mzeitler/openstrom/schematic/source - draft/Altium-CPU-board-multi/Cross-section-sketch2.PcbDoc.htm

Reporting Options

# File in Previous Format

Date | : | 24.06.2016
Time | : | 16:26:15
Filename | : | C:\Users\Matthias E. Zeitler\Documents\Business\Open Strom\Github\openstrom\schematic\source - draft\Altium-CPU-board-multi\Cross-section-sketch2.PcbDoc

Version | Warning

This file was generated by an earlier version of the software
