mzeitler/openstrom/docs/OpenStrom - Pitch - Oct 2015.pdf

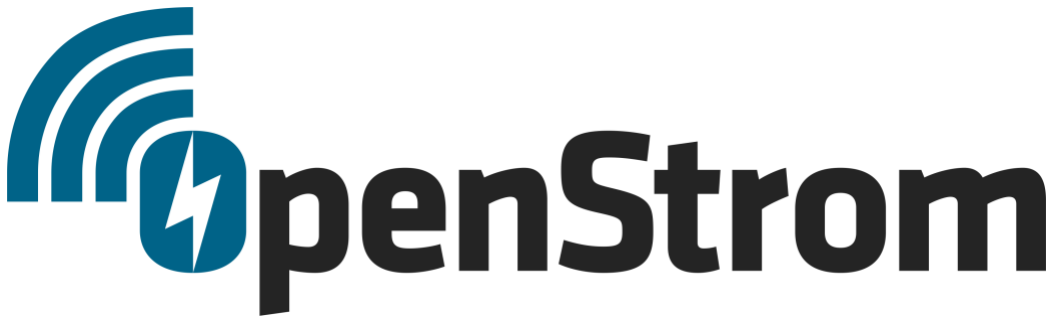
[picture p21: figure]

# The Open Hardware Smart Meter

# that powers the smart energy revolution

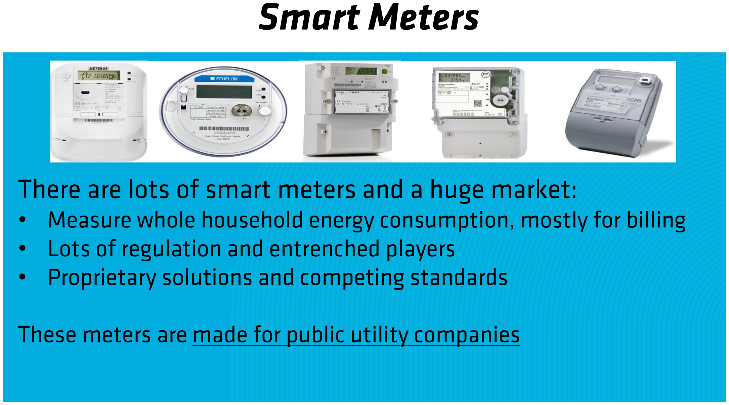
[picture p22: page 2]

•••

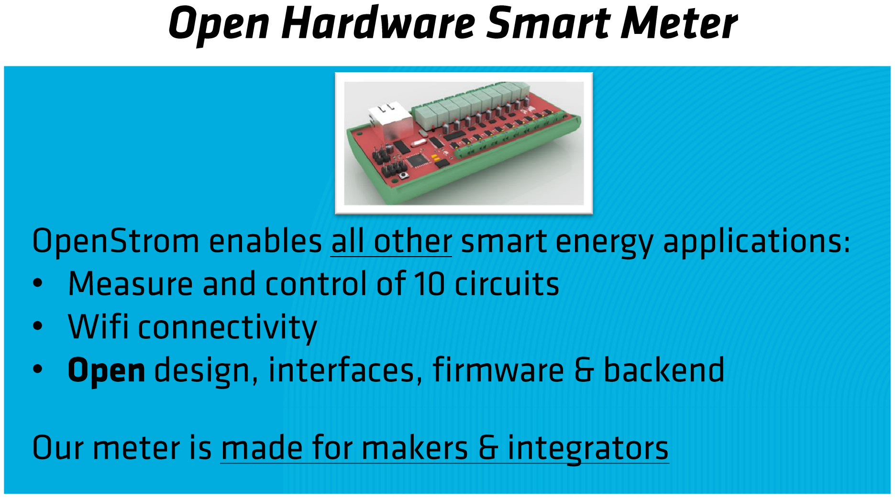
[picture p23: page 3]

•••

Component | Characteristics
MCU | 80 MHz 512k kB + 128 MB
Connectivity | LAN, Wifi ZigBee
Sensors | Voltage, current, mean active power, mean reactive power, voltage frequency, power factor, phase angle between voltage and current, mean apparent power 90 - 250 V AC 0 – 40A 7.4 kHz sampling
Relays (10x) | Switching up to 40A at 250V, max. 10kW
Form factor | DIN rail compatible housing (for mounting inside fuse box)

### Operating temperature range: 0°C to 85°C (commercial)

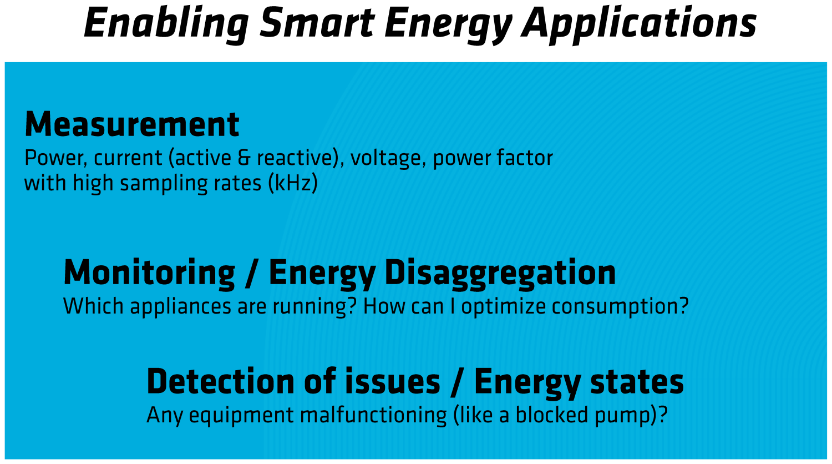
[picture p24: page 5]

•••

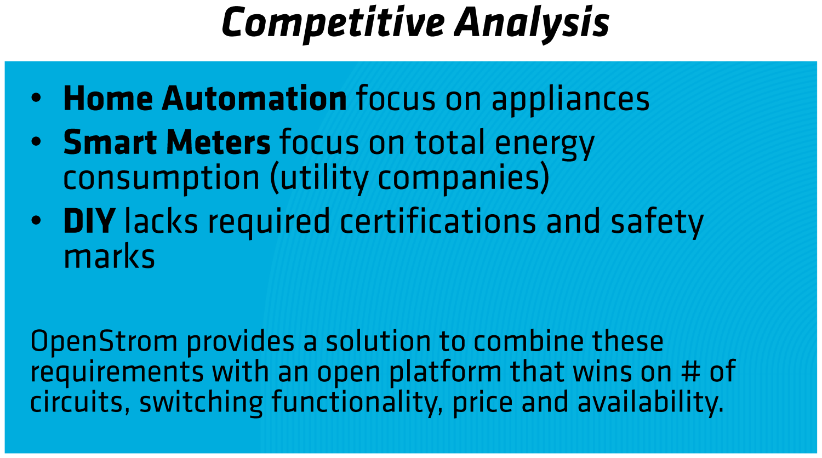
[picture p25: page 6]

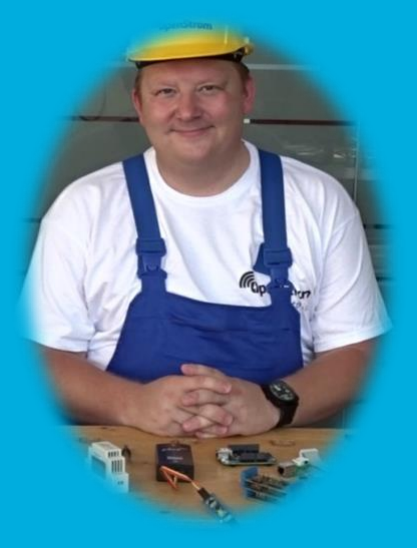
[picture p26: figure]
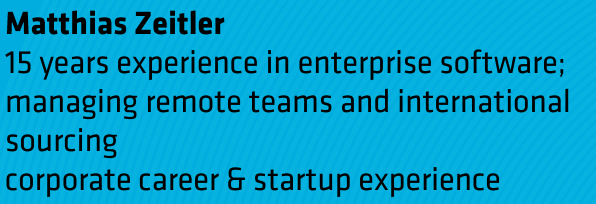
[picture p27: figure]

Engineering team to build prototype:
Tony Tachev, 20 years experience as embedded engineer designing with microcontrollers Franklin Francis, 5 years experience with firmware development and prototyping
plus identified candidates for software development

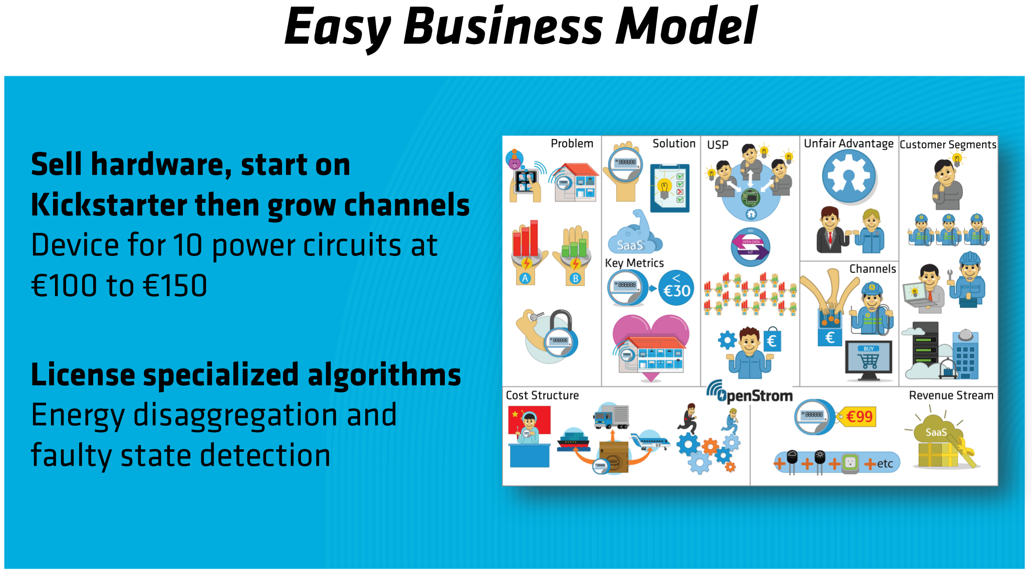
[picture p28: page 8]
