mzeitler/openstrom/housing/v0.1 - initial ideas/1 (1).JPG

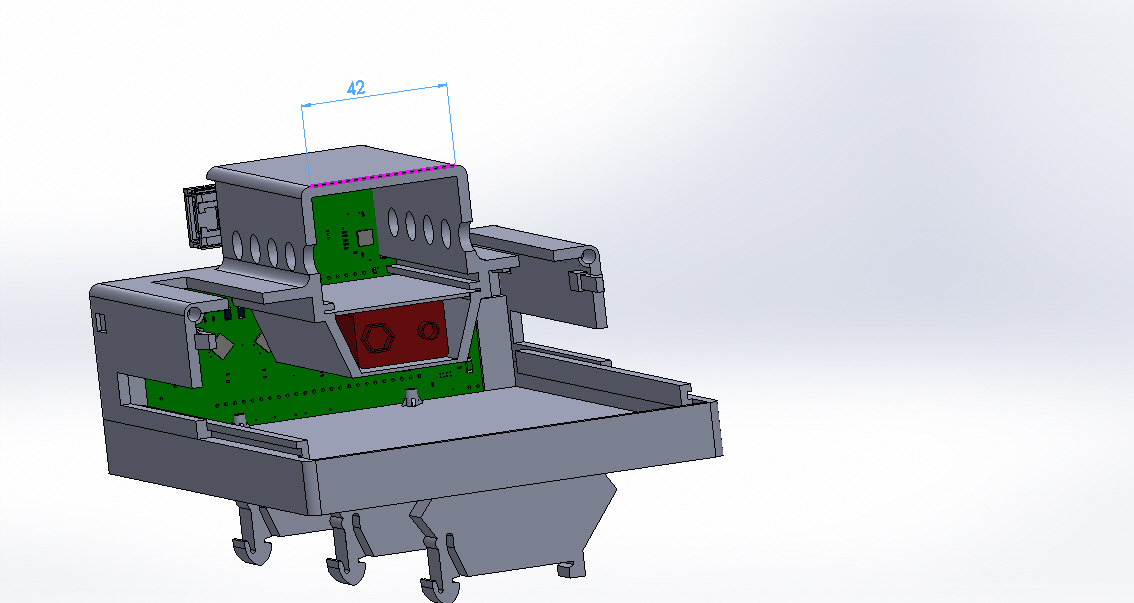
housing/v0.1 - initial ideas/1 (1).JPG
