mzeitler/openstrom/housing/v0.1 - initial ideas/2.jpg

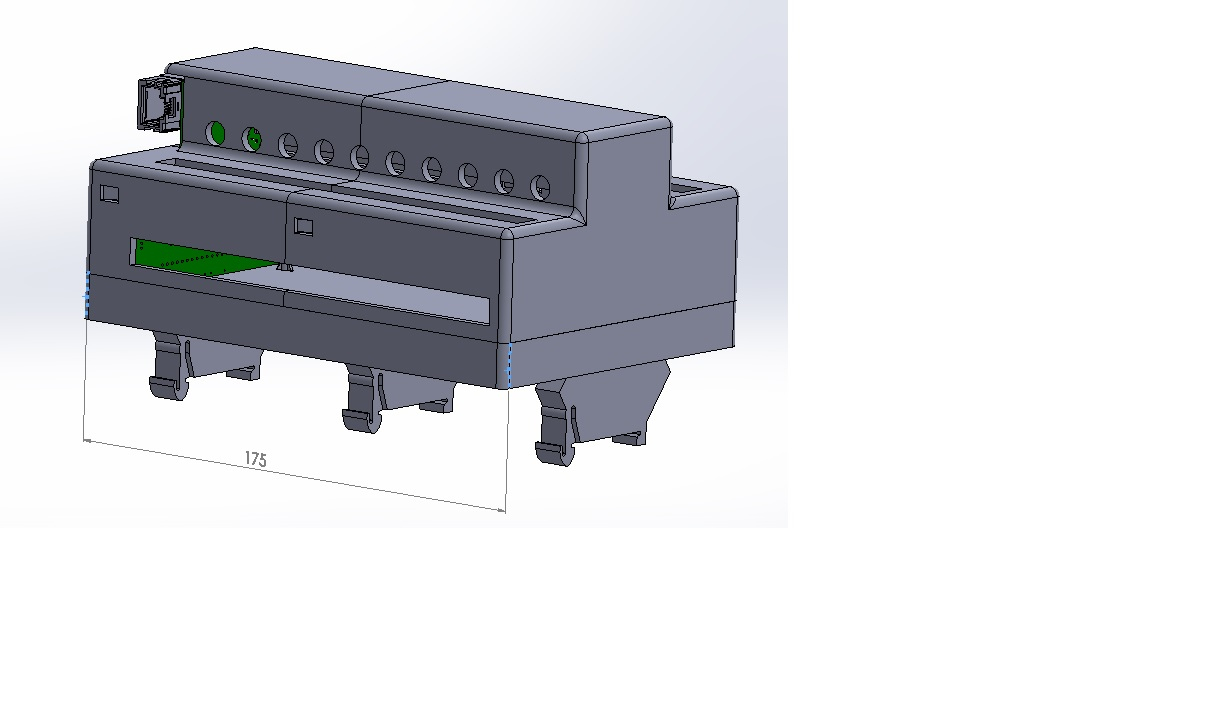
housing/v0.1 - initial ideas/2.jpg
