mzeitler/openstrom/housing/v0.1 - initial ideas/3.JPG

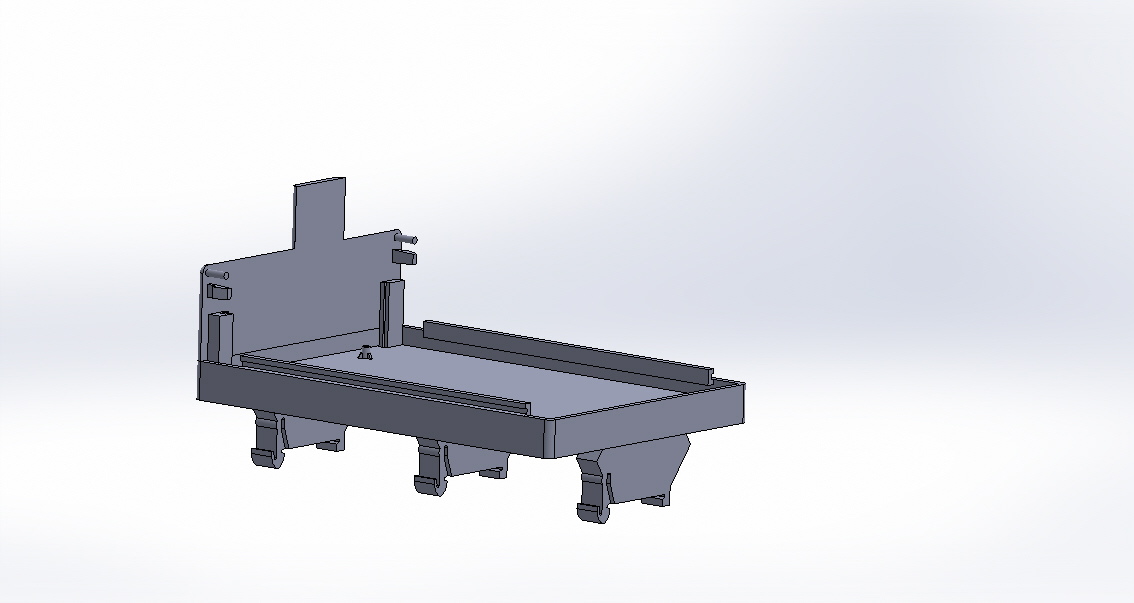
housing/v0.1 - initial ideas/3.JPG
