mzeitler/openstrom/housing/v0.1 - initial ideas/4.JPG

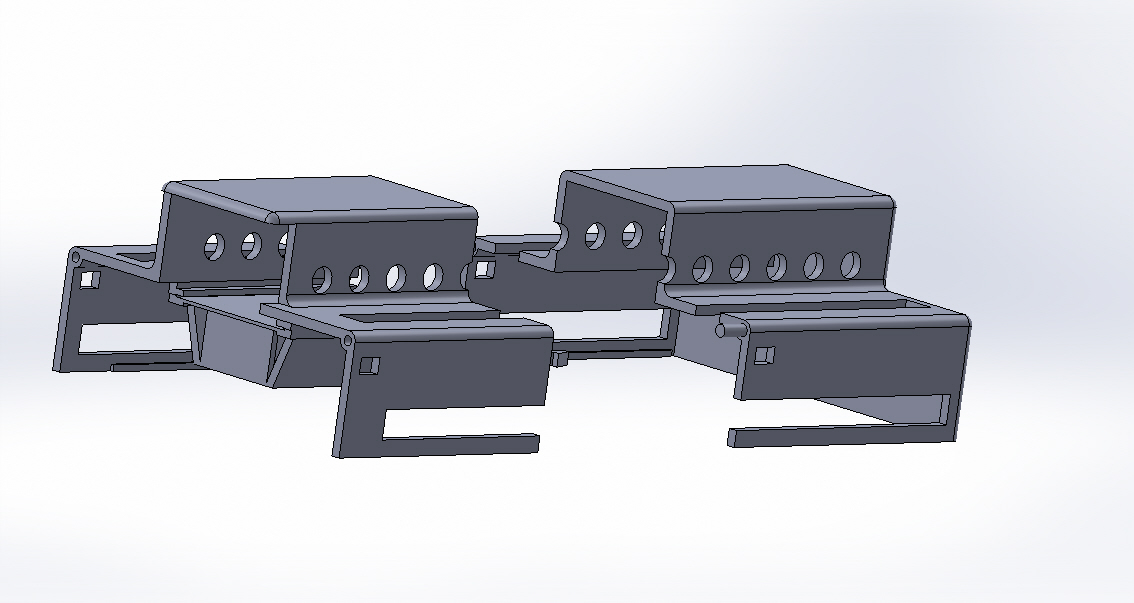
housing/v0.1 - initial ideas/4.JPG
