mzeitler/openstrom/housing/v0.1 - initial ideas/5.JPG

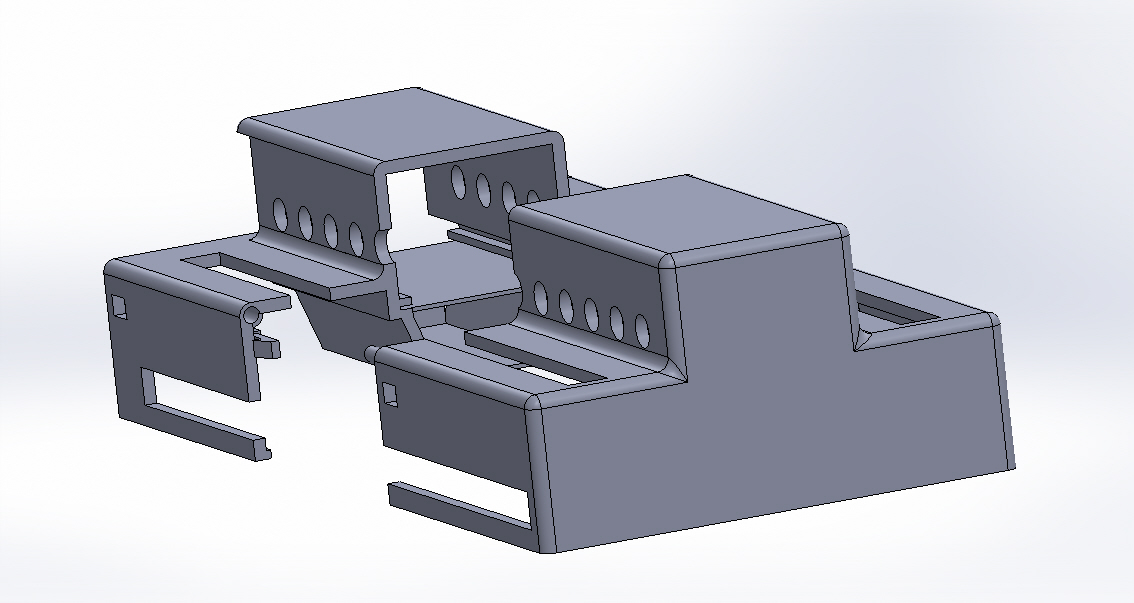
housing/v0.1 - initial ideas/5.JPG
