mzeitler/openstrom/housing/v0.1 - initial ideas/CT_BOARD.jpg

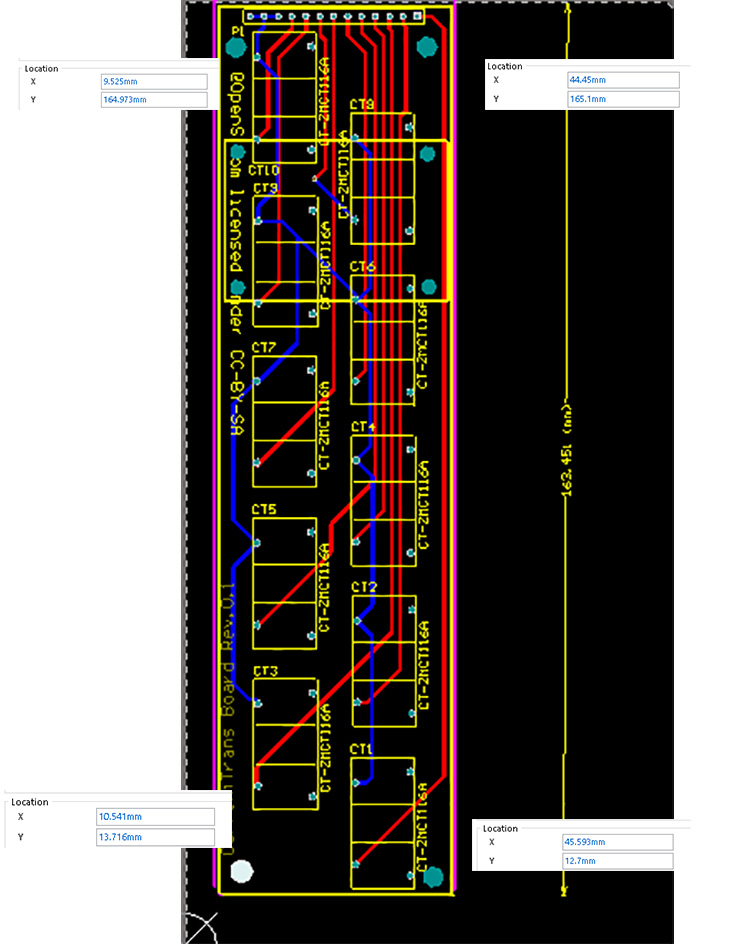
housing/v0.1 - initial ideas/CT_BOARD.jpg
