mzeitler/openstrom/housing/v0.1 - initial ideas/Final Exploded view-1.JPG

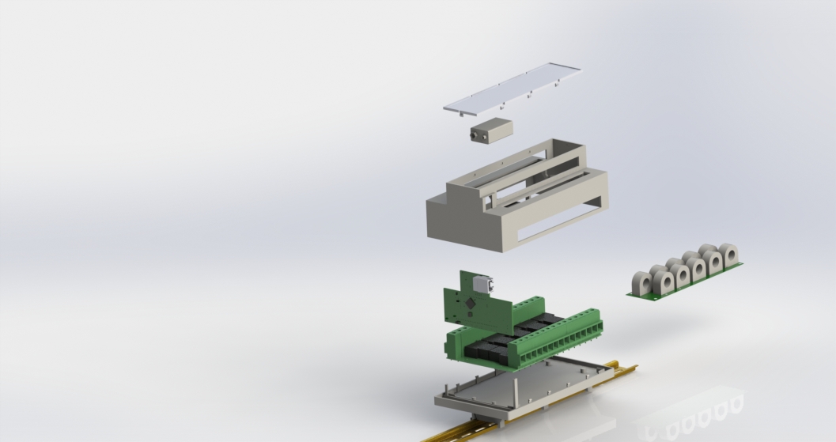
housing/v0.1 - initial ideas/Final Exploded view-1.JPG
