mzeitler/openstrom/housing/v0.1 - initial ideas/Final Exploded view-2.JPG

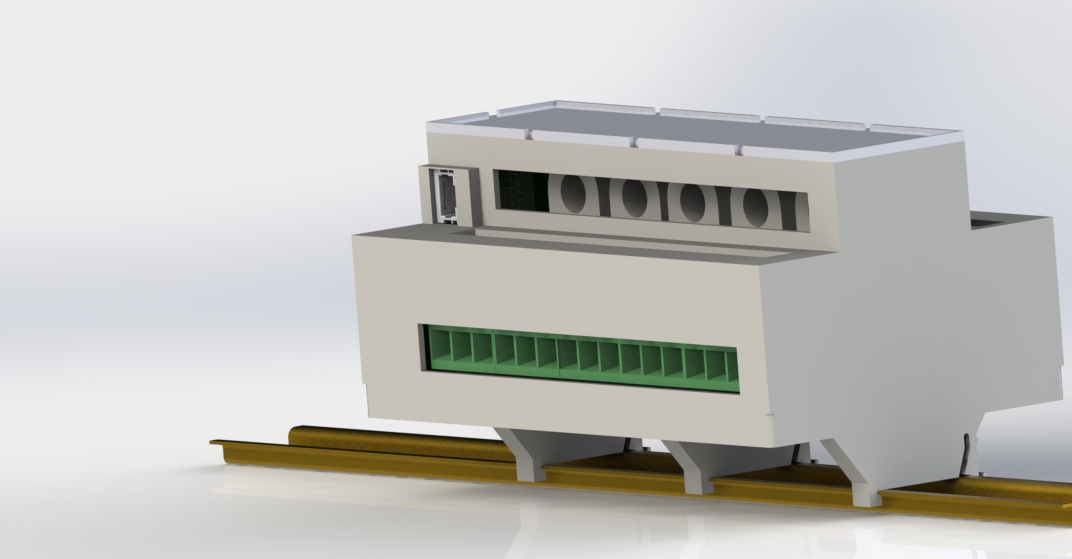
housing/v0.1 - initial ideas/Final Exploded view-2.JPG
