mzeitler/openstrom/housing/v0.1 - initial ideas/Relay_BOARD_H.jpg

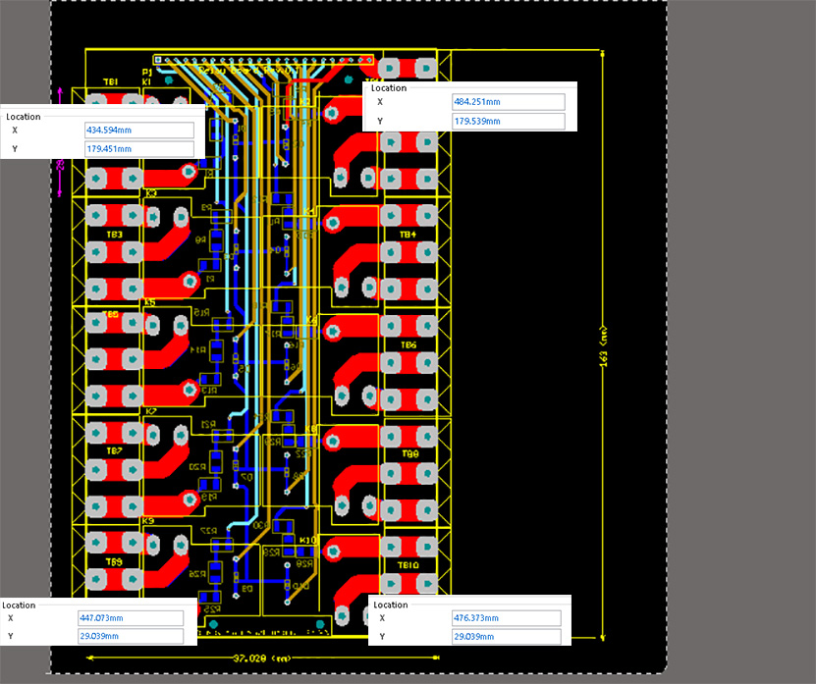
housing/v0.1 - initial ideas/Relay_BOARD_H.jpg
