mzeitler/openstrom/housing/v0.2 - design for prototpye/Ethernet Port View.JPG

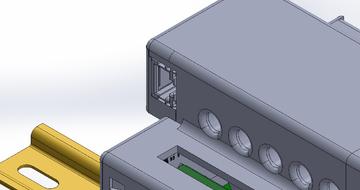
housing/v0.2 - design for prototpye/Ethernet Port View.JPG
