mzeitler/openstrom/housing/v0.2 - design for prototpye/Part2.JPG

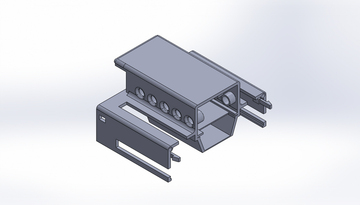
housing/v0.2 - design for prototpye/Part2.JPG
