mzeitler/openstrom/housing/v0.2 - design for prototpye/Part3.JPG

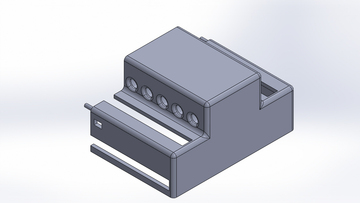
housing/v0.2 - design for prototpye/Part3.JPG
