mzeitler/openstrom/housing/v0.3 - prototype/CIMG8475.JPG

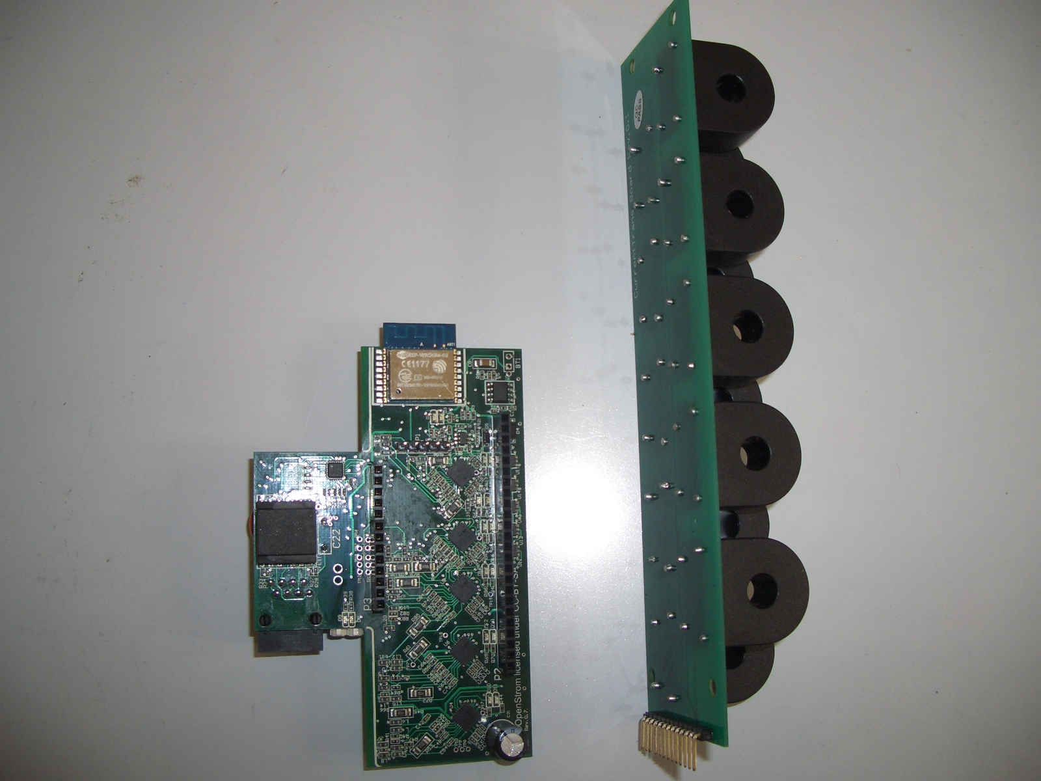
housing/v0.3 - prototype/CIMG8475.JPG
