mzeitler/openstrom/housing/v0.3 - prototype/CIMG8476.JPG

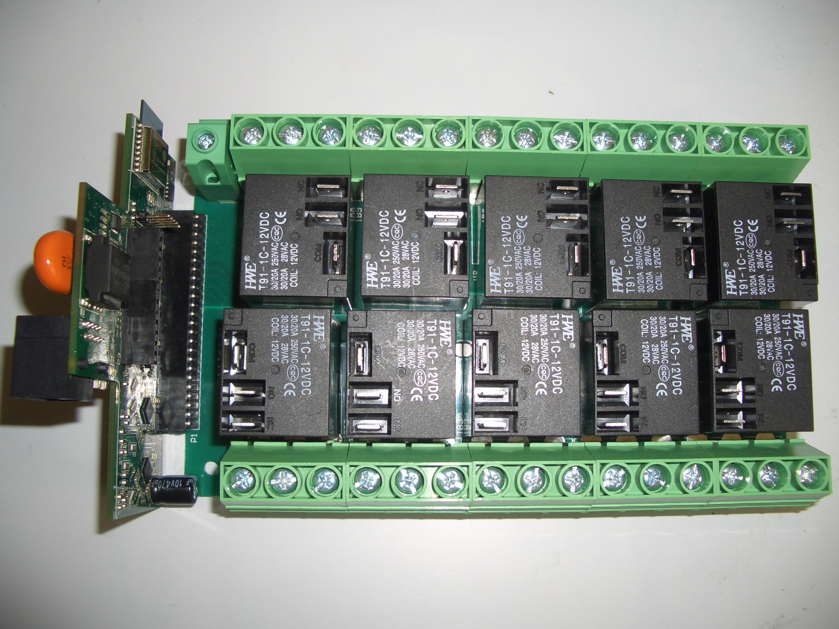
housing/v0.3 - prototype/CIMG8476.JPG
