mzeitler/openstrom/housing/v0.3 - prototype/CIMG8477.JPG

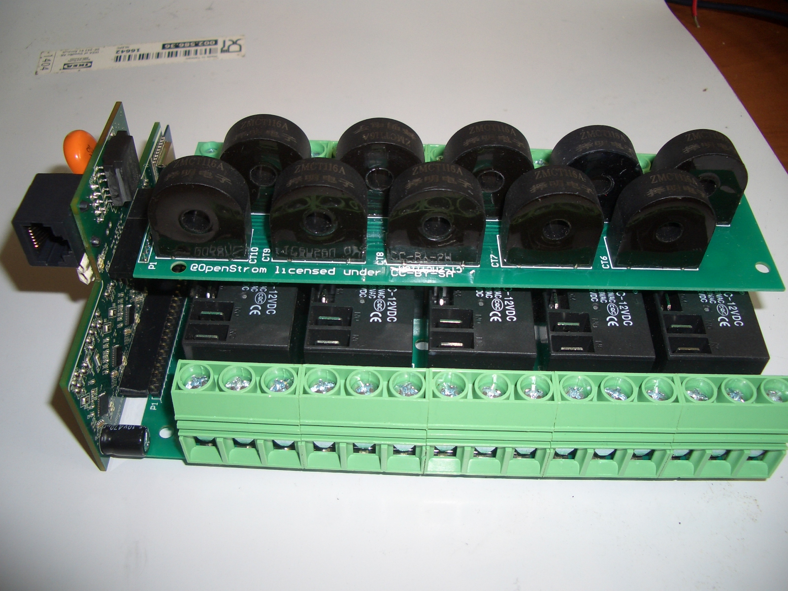
housing/v0.3 - prototype/CIMG8477.JPG
