mzeitler/openstrom/housing/v0.3 - prototype/CIMG8479.JPG

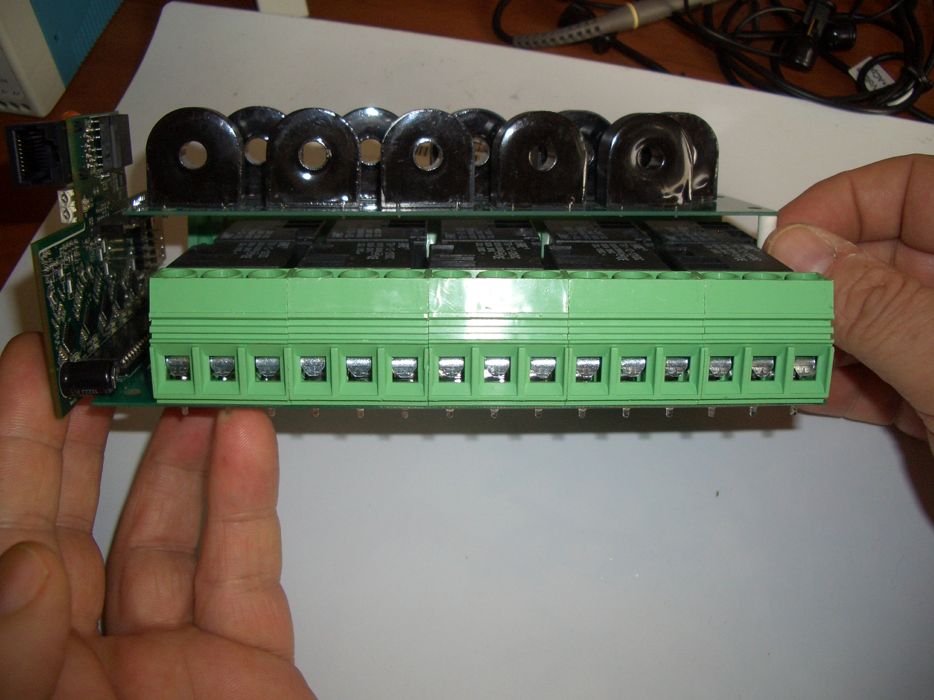
housing/v0.3 - prototype/CIMG8479.JPG
