mzeitler/openstrom/housing/v0.4 - prototype 2/18955070_1875733002680077_9011409751416302212_o.jpg

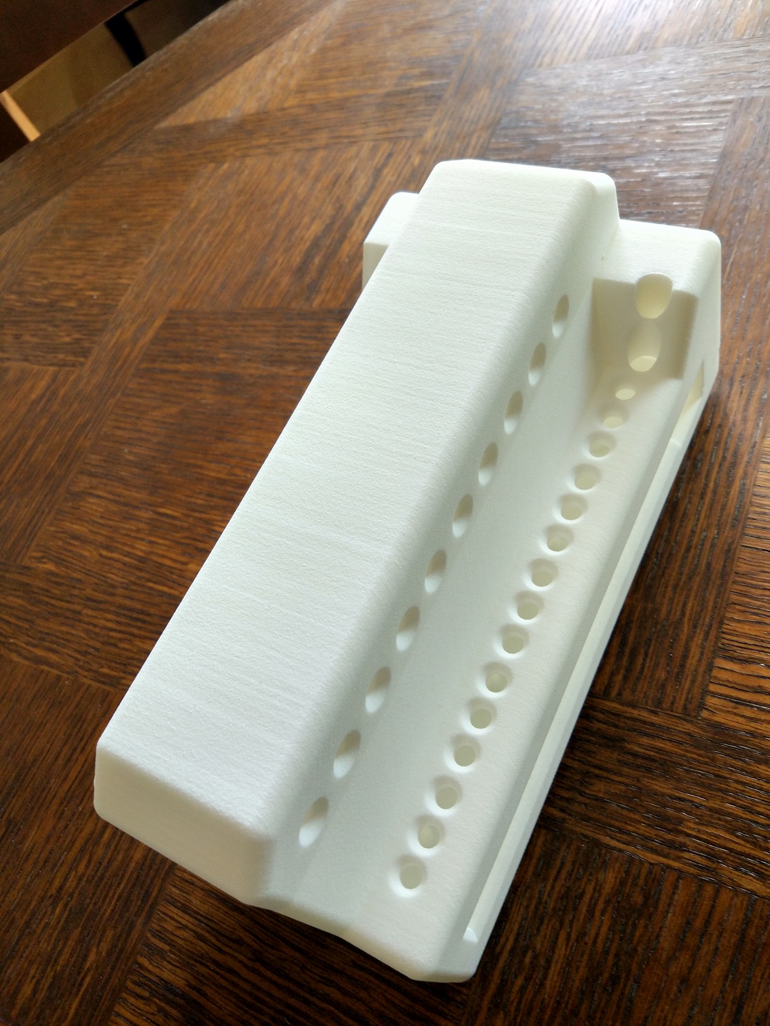
housing/v0.4 - prototype 2/18955070_1875733002680077_9011409751416302212_o.jpg
