mzeitler/openstrom/housing/v0.4a - Lasercut/18891693_1875733032680074_797341241410242619_o.jpg

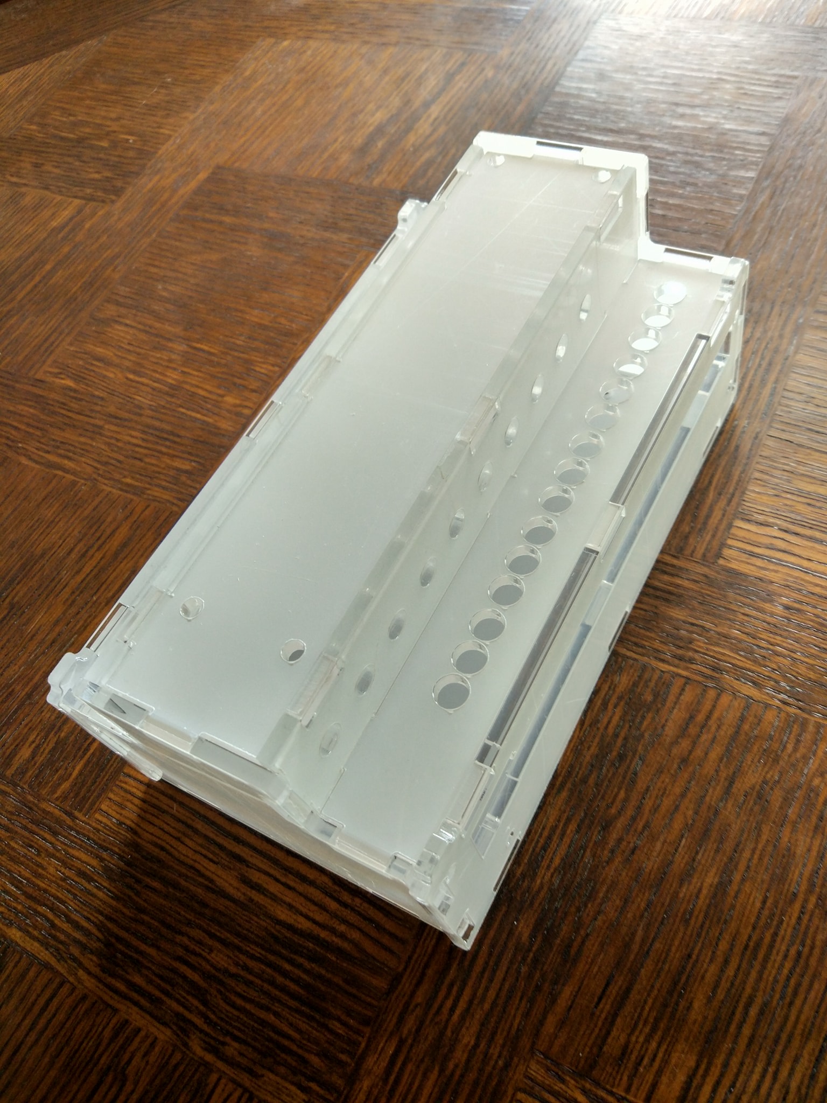
housing/v0.4a - Lasercut/18891693_1875733032680074_797341241410242619_o.jpg
