mzeitler/openstrom/housing/v0.4 - prototype 2/assembled/2017-06-19 10.52.02.jpg

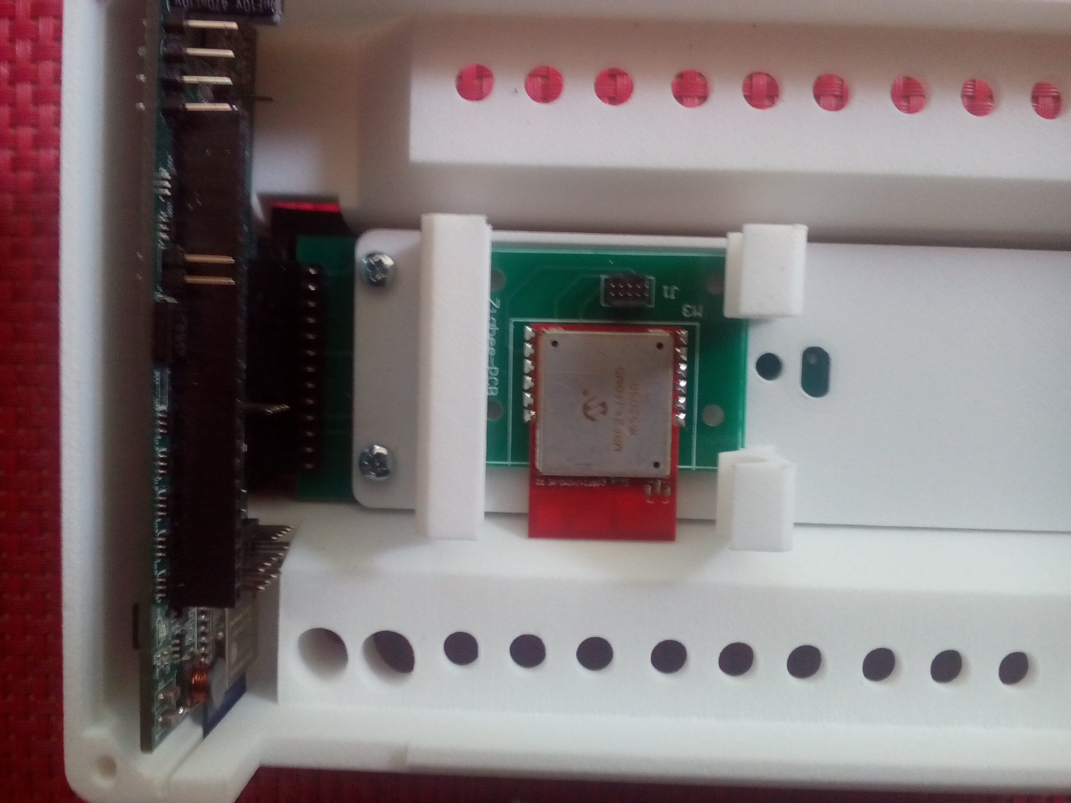
housing/v0.4 - prototype 2/assembled/2017-06-19 10.52.02.jpg
