mzeitler/openstrom/housing/v0.4 - prototype 2/assembled/2017-06-19 11.23.50.jpg

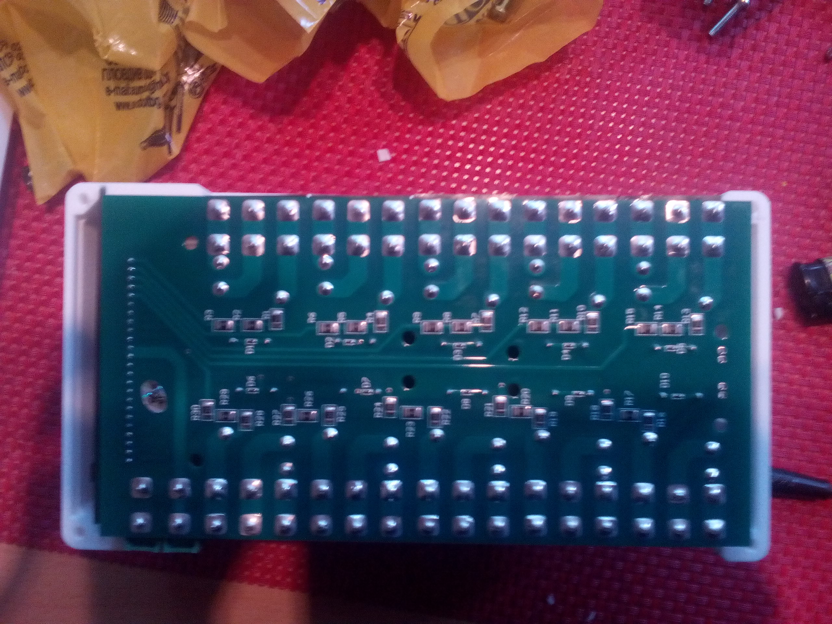
housing/v0.4 - prototype 2/assembled/2017-06-19 11.23.50.jpg
