mzeitler/openstrom/housing/v0.4 - prototype 2/assembled/2017-06-19 11.59.24.jpg

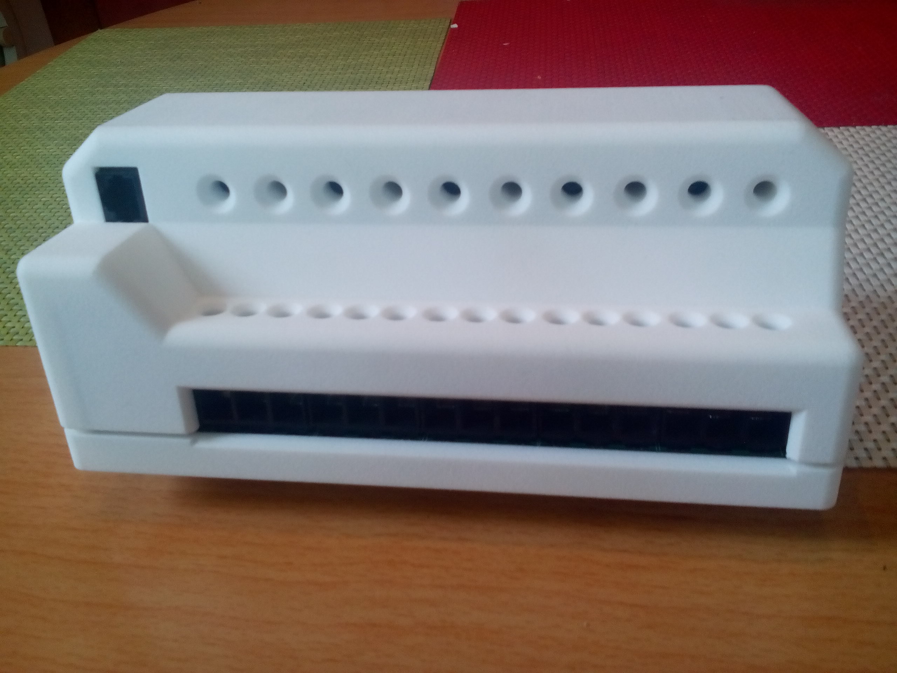
housing/v0.4 - prototype 2/assembled/2017-06-19 11.59.24.jpg
