mzeitler/openstrom/schematic/source - draft/PDF - for reference only/RelayBoard-Sch-multi.pdf

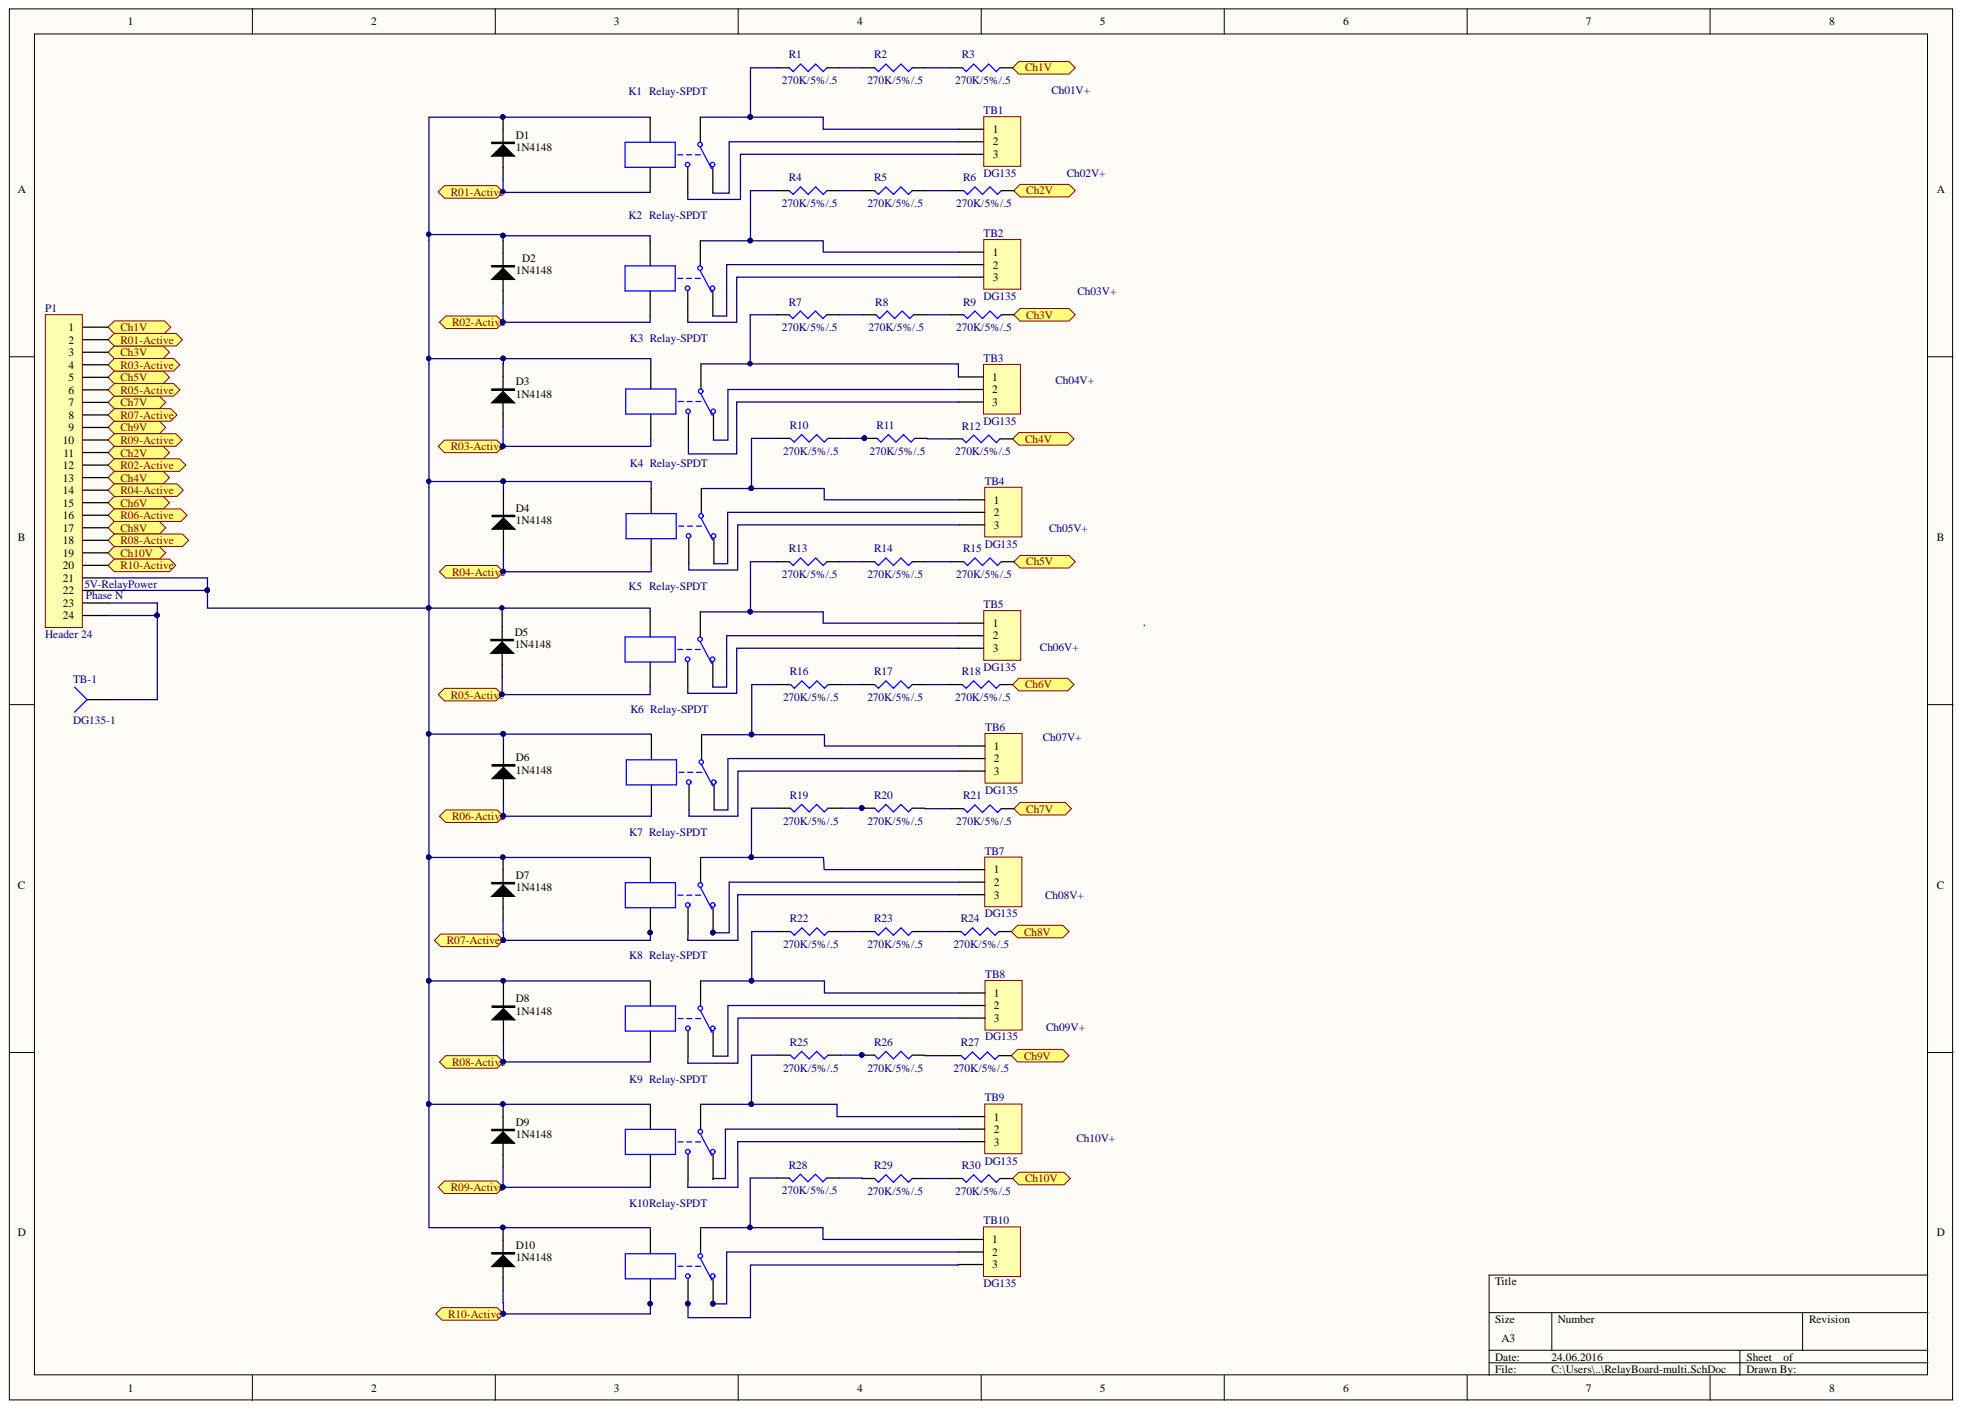
[picture p106: page 1]

5V-RelayPower
Phase N
