mzeitler/openstrom/housing/v0.1 - initial ideas/(Top Panel _2 - Sheet1.pdf

8 | 7 | 6 | 5 | 4 | 3 | 2 | 1

E

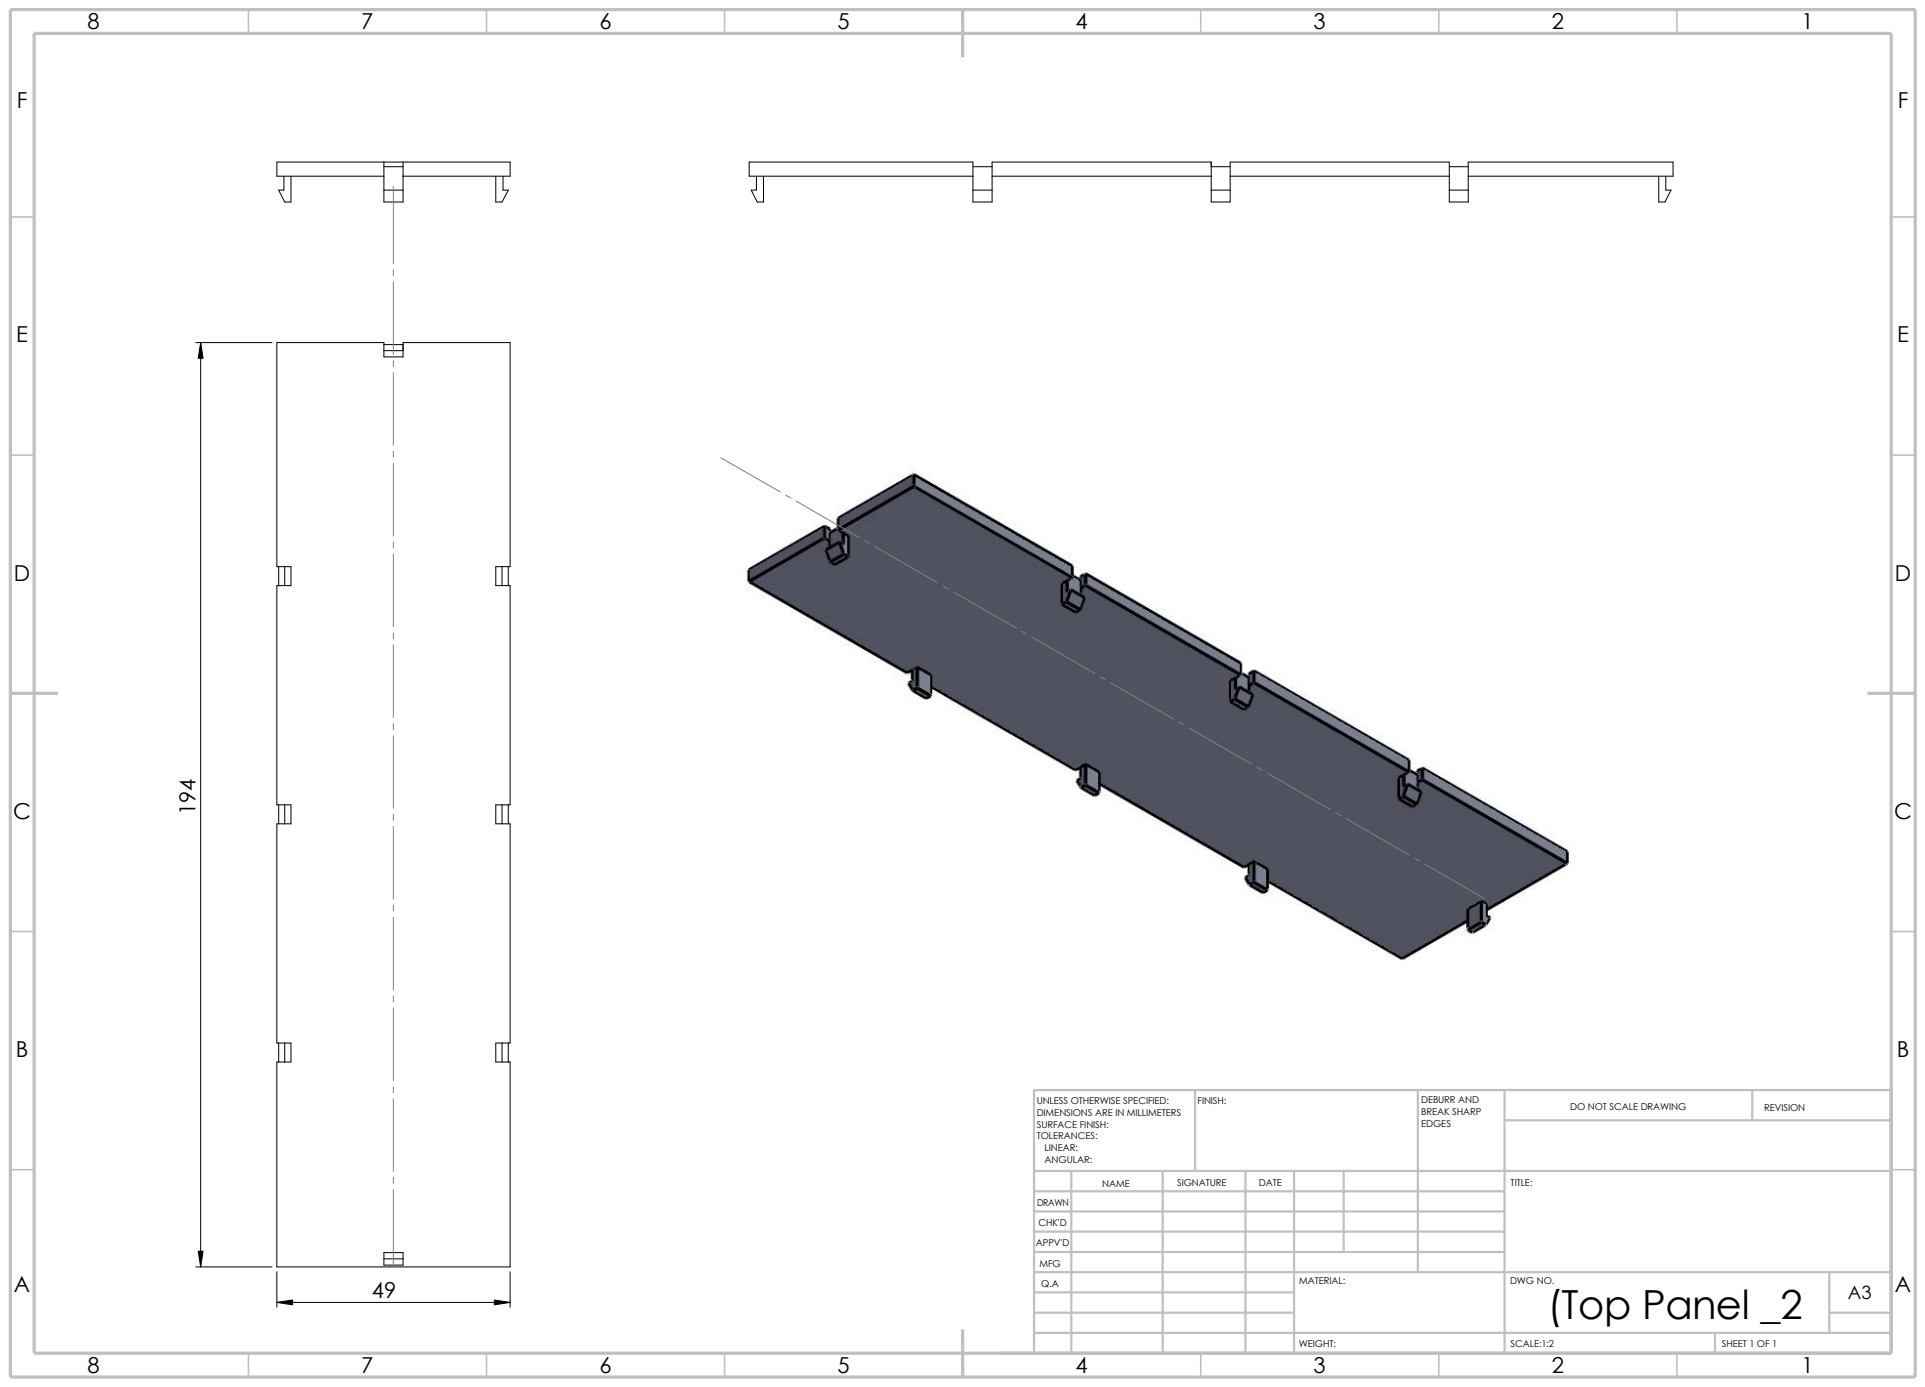
[picture p107: page 1]
WEIGHT:; SCALE:1:2; SHEET 1 OF 1; REVISION; FINISH:; EDGES; DEBURR AND BREAK SHARP

DO NOT SCALE DRAWING UNLESS OTHERWISE SPECIFIED:
DIMENSIONS ARE IN MILLIMETERS
SURFACE FINISH:
TOLERANCES:
LINEAR:
ANGULAR:

NAME | SIGNATURE | DATE | | | | TITLE:

DRAWN

CHK'D

APPV'D

MFG
Q.A | | | | MATERIAL: | DWG NO. | A3

(Top Panel _2 ⁴⁹
