mzeitler/openstrom/housing/v0.1 - initial ideas/base - Sheet1.pdf

8 | 7 | 6 | 5 | 4 | 3 | 2 | 1

E

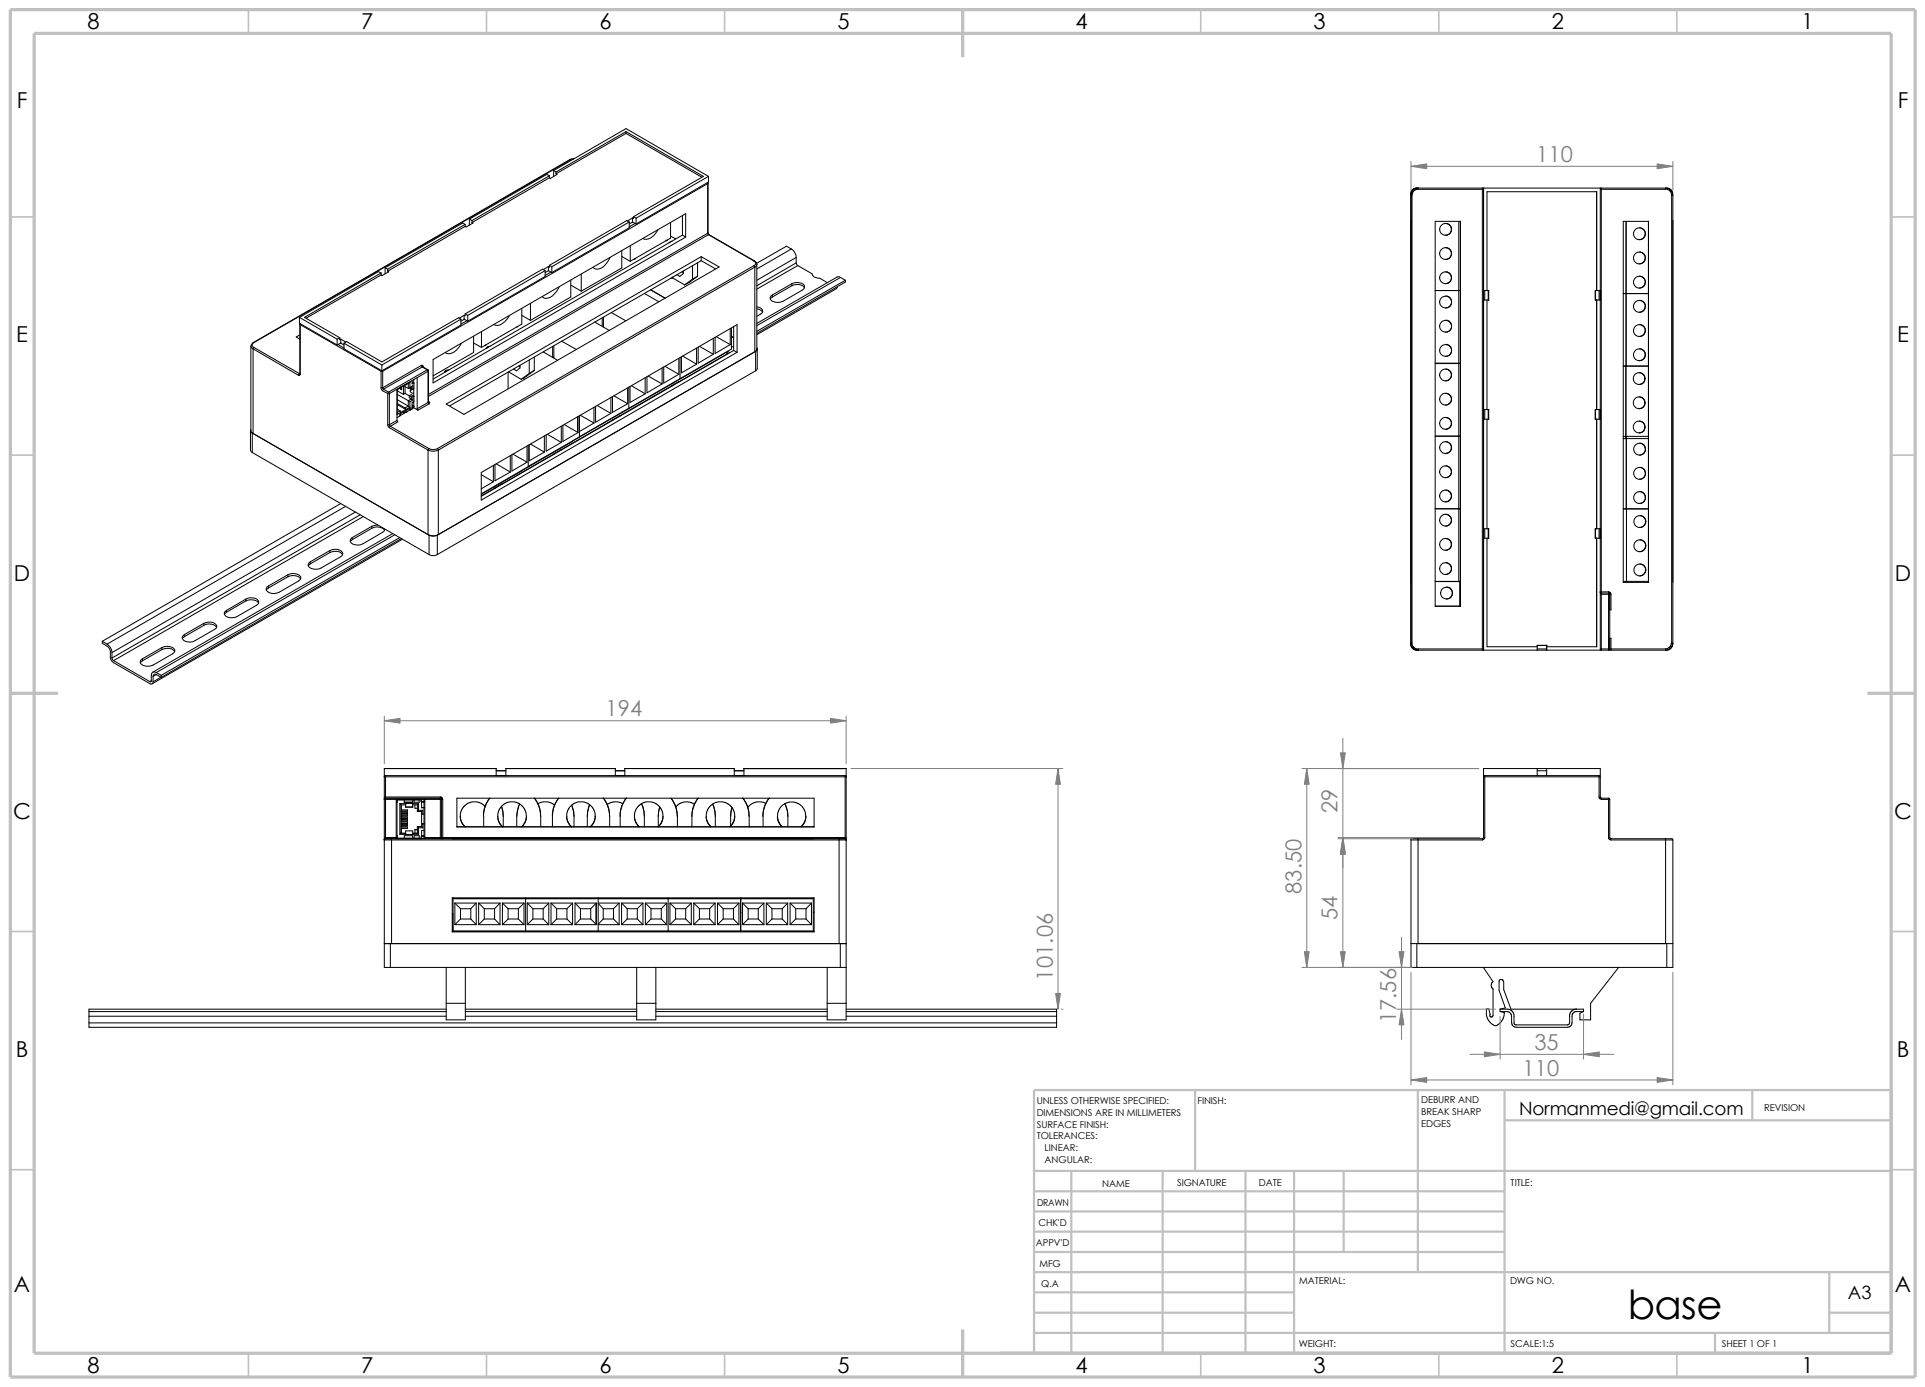
[picture p108: page 1]
WEIGHT:; SCALE:1:5; SHEET 1 OF 1; Normanmedi@gmail.com; REVISION UNLESS OTHERWISE SPECIFIED:

DIMENSIONS ARE IN MILLIMETERS SURFACE FINISH: TOLERANCES: LINEAR: ANGULAR: | FINISH: | DEBURR AND BREAK SHARP EDGES

NAME | SIGNATURE | DATE | | | | TITLE:

DRAWN

CHK'D

APPV'D

MFG

Q.A | | | | MATERIAL: | DWG NO. base | A3
