mzeitler/openstrom/housing/v0.1 - initial ideas/main_5 - Sheet1.pdf

8 | 7 | 6 | 5 | 4 | 3 | 2 | 1

E

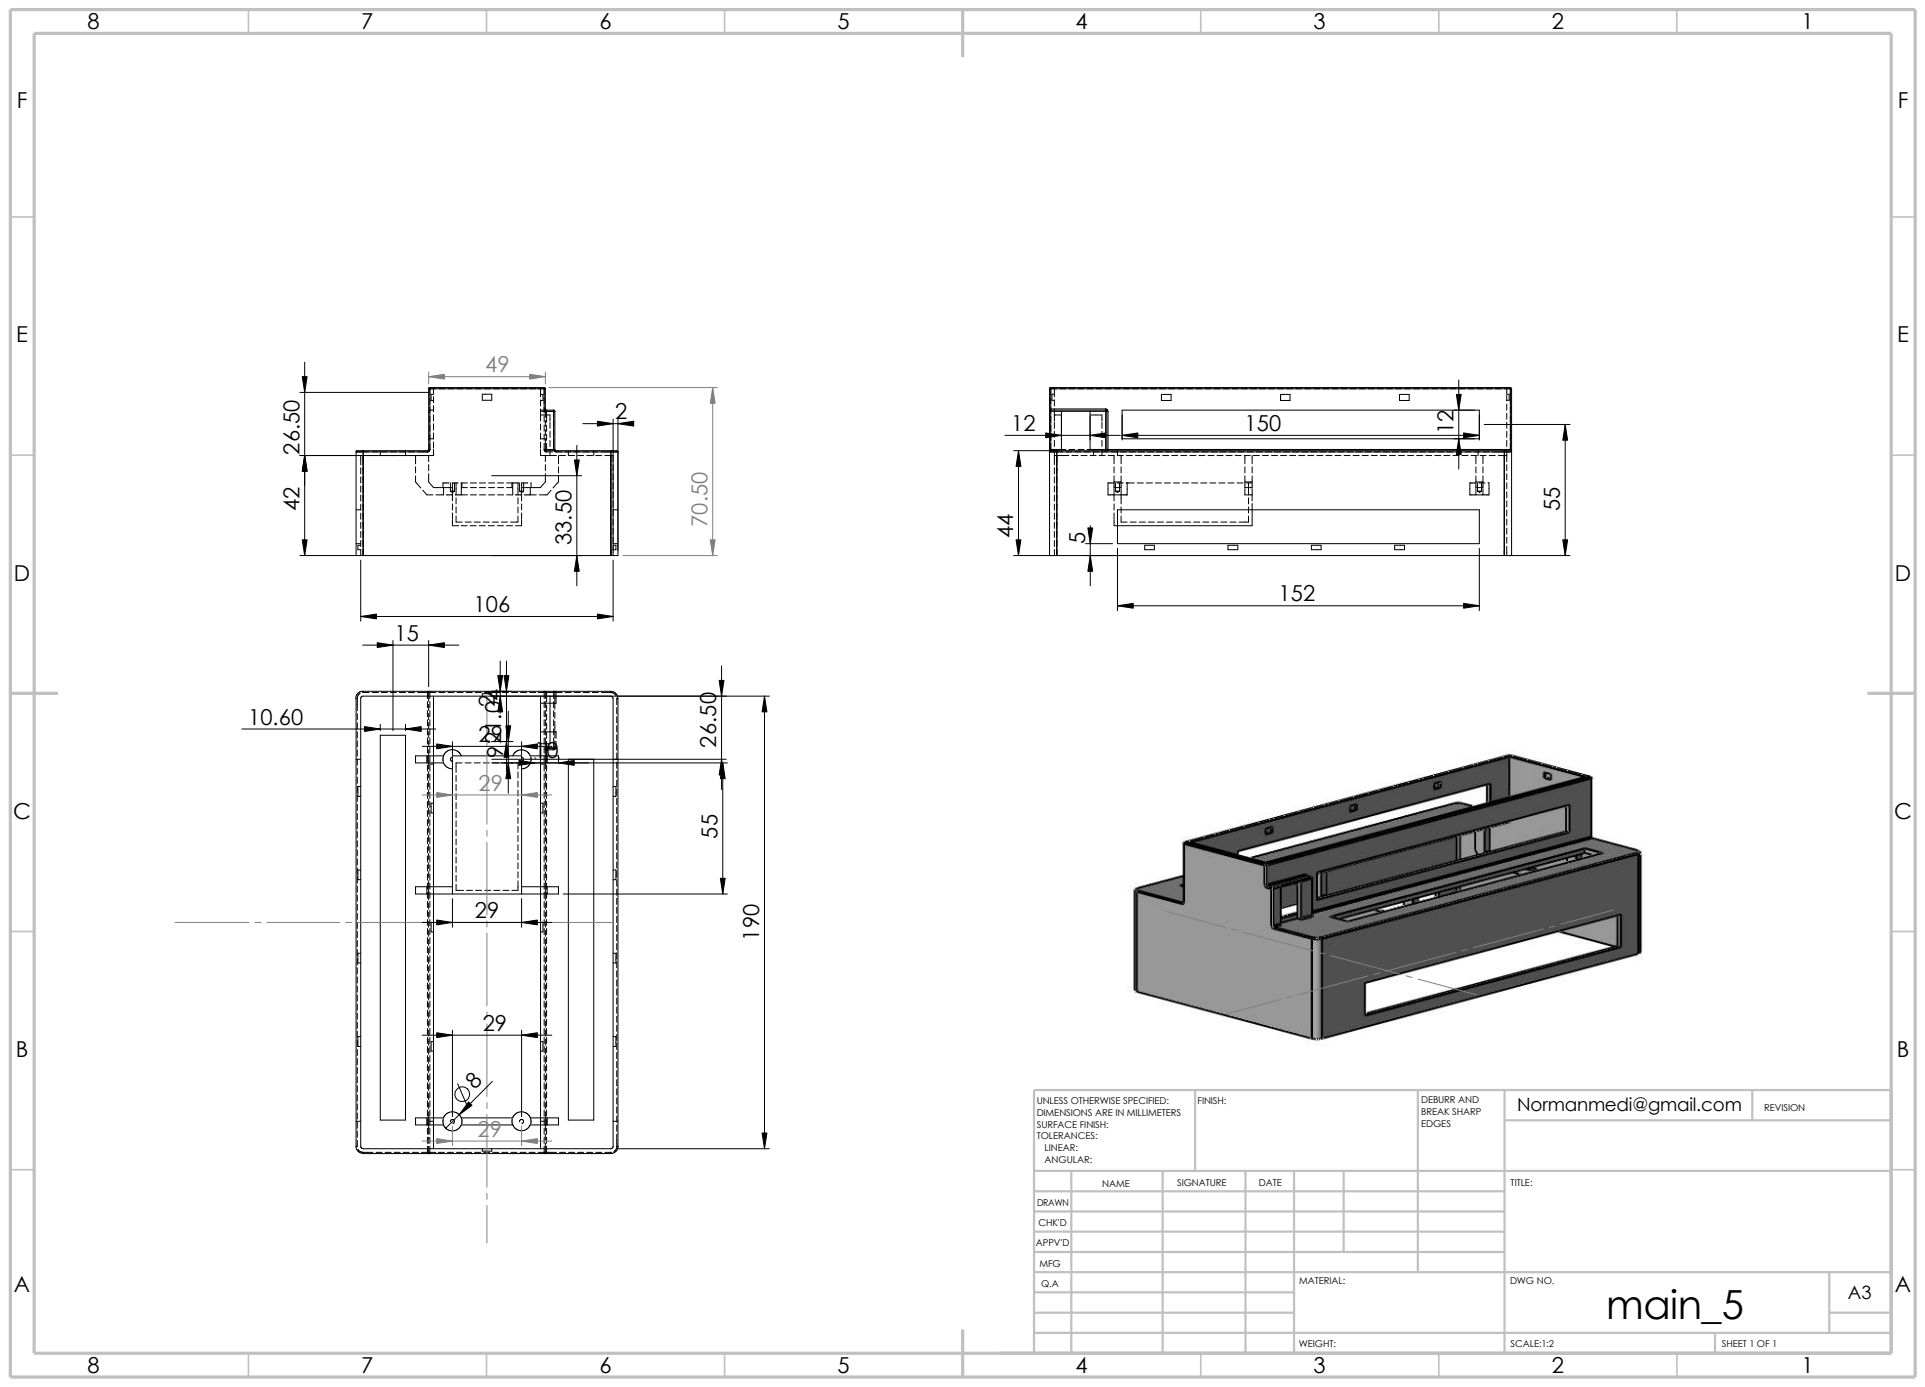
[picture p109: page 1]
WEIGHT:; SCALE:1:2; SHEET 1 OF 1; Normanmedi@gmail.com; REVISION UNLESS OTHERWISE SPECIFIED:

29
10

DIMENSIONS ARE IN MILLIMETERS SURFACE FINISH: TOLERANCES: LINEAR: ANGULAR: | FINISH: | DEBURR AND BREAK SHARP EDGES

NAME | SIGNATURE | DATE | | | | TITLE:

DRAWN

CHK'D

APPV'D

MFG

Q.A | | | | MATERIAL: | DWG NO. main_5 | A3
