mzeitler/openstrom/housing/v0.1 - initial ideas/Part2-2 - Sheet1.pdf

2 | 1

B

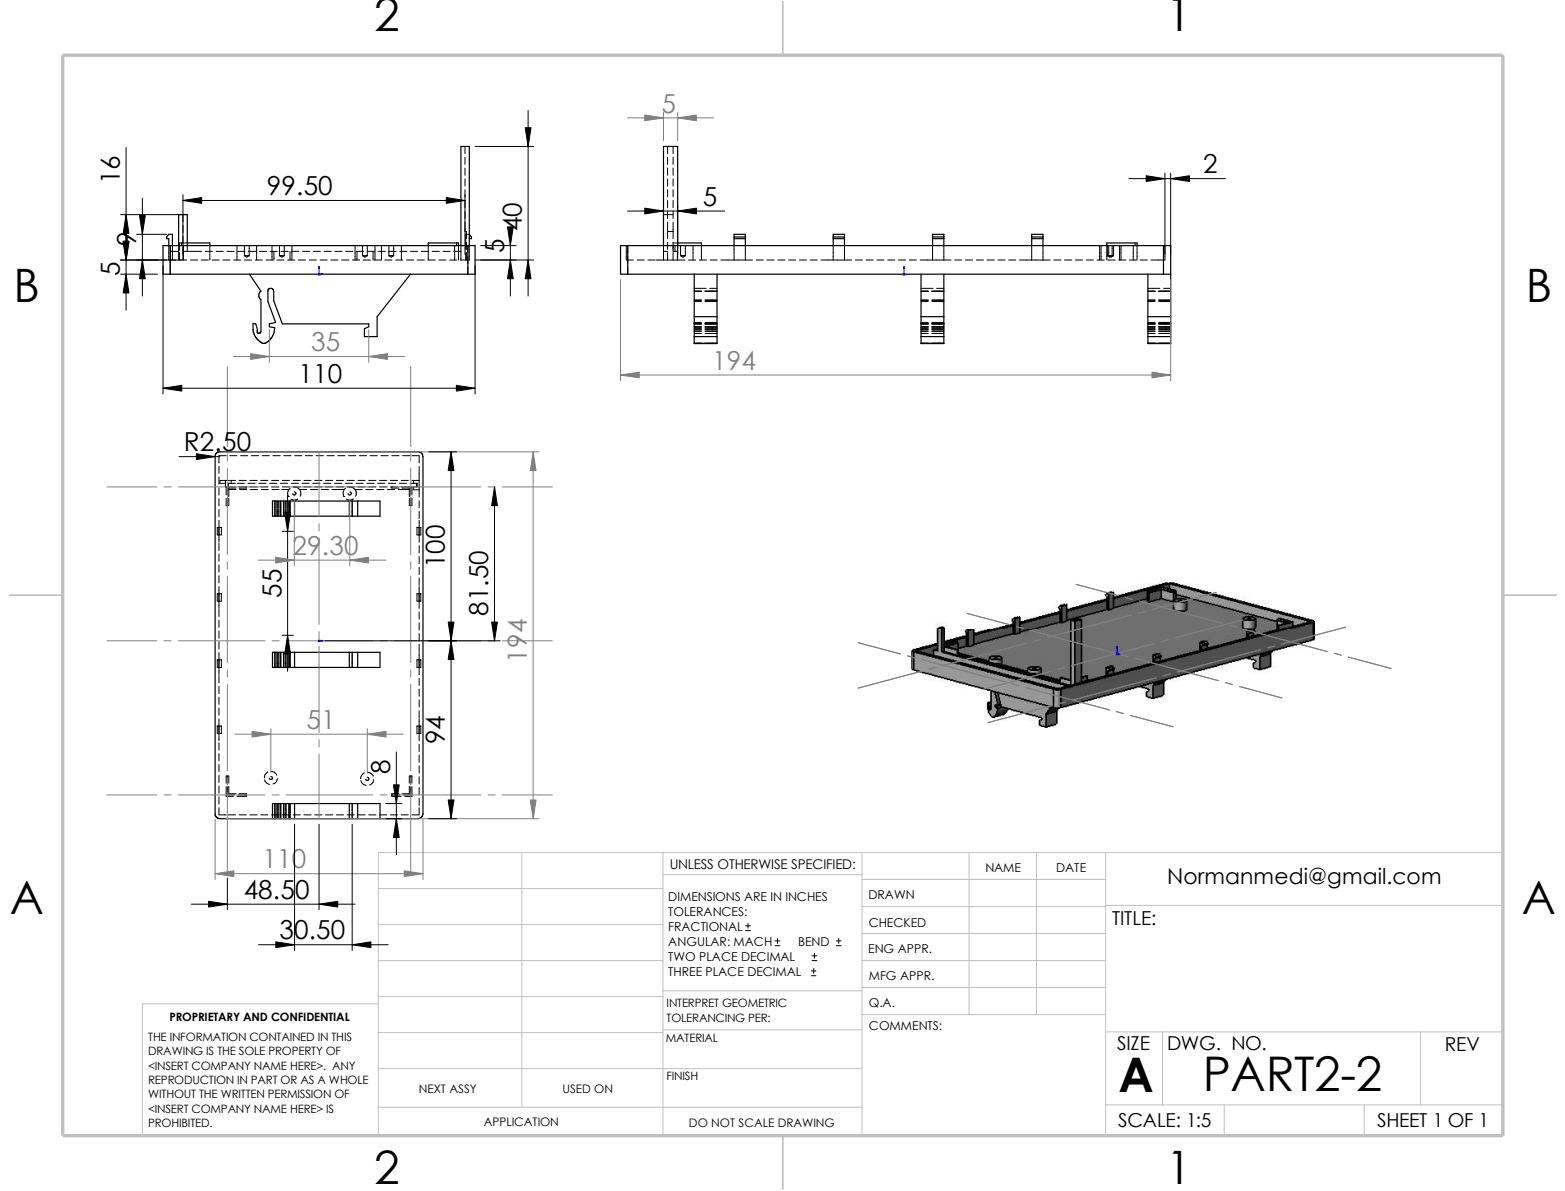
[picture p110: page 1]
DRAWN; COMMENTS:

UNLESS OTHERWISE SPECIFIED: | NAME | DATE | Normanmedi@gmail.com

48.50 | | DIMENSIONS ARE IN INCHES TOLERANCES: FRACTIONAL ANGULAR: MACH BEND TWO PLACE DECIMAL THREE PLACE DECIMAL

CHECKED | | TITLE:

ENG APPR.

MFG APPR.

INTERPRET GEOMETRIC TOLERANCING PER: | Q.A.

PROPRIETARY AND CONFIDENTIAL
THE INFORMATION CONTAINED IN THIS
DRAWING IS THE SOLE PROPERTY OF
<INSERT COMPANY NAME HERE>. ANY
REPRODUCTION IN PART OR AS A WHOLE
WITHOUT THE WRITTEN PERMISSION OF
<INSERT COMPANY NAME HERE> IS
PROHIBITED.

MATERIAL | | SIZE A | DWG. NO. PART2-2 | REV

NEXT ASSY | USED ON | FINISH

APPLICATION | DO NOT SCALE DRAWING | | SCALE: 1:5 | | SHEET 1 OF 1
