mzeitler/openstrom/schematic/source - draft/PDF - for reference only/CurrentTrans-board--Sch-multi.pdf

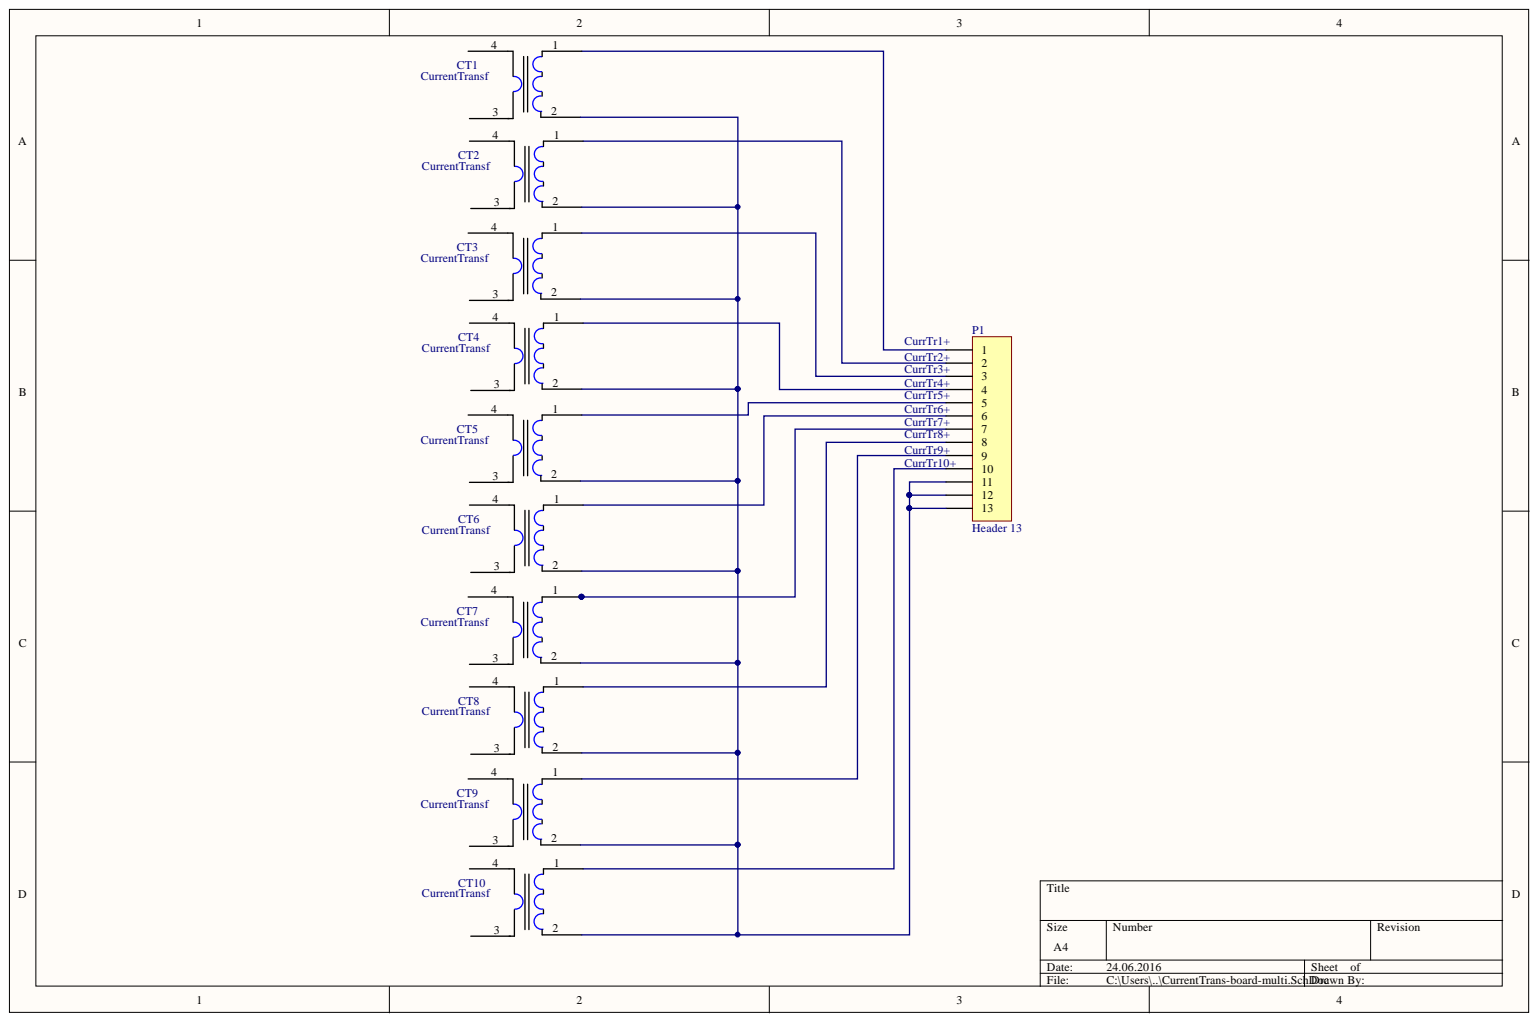
[picture p112: page 1]

CurrTr2+
CurrTr3+
CurrTr4+ CurrTr5+

CurrTr6+ CurrTr7+

CurrTr8+
CurrTr9+
CurrTr10+
