mzeitler/openstrom/schematic/source - draft/PDF - for reference only/RelayBoard-multi.pdf

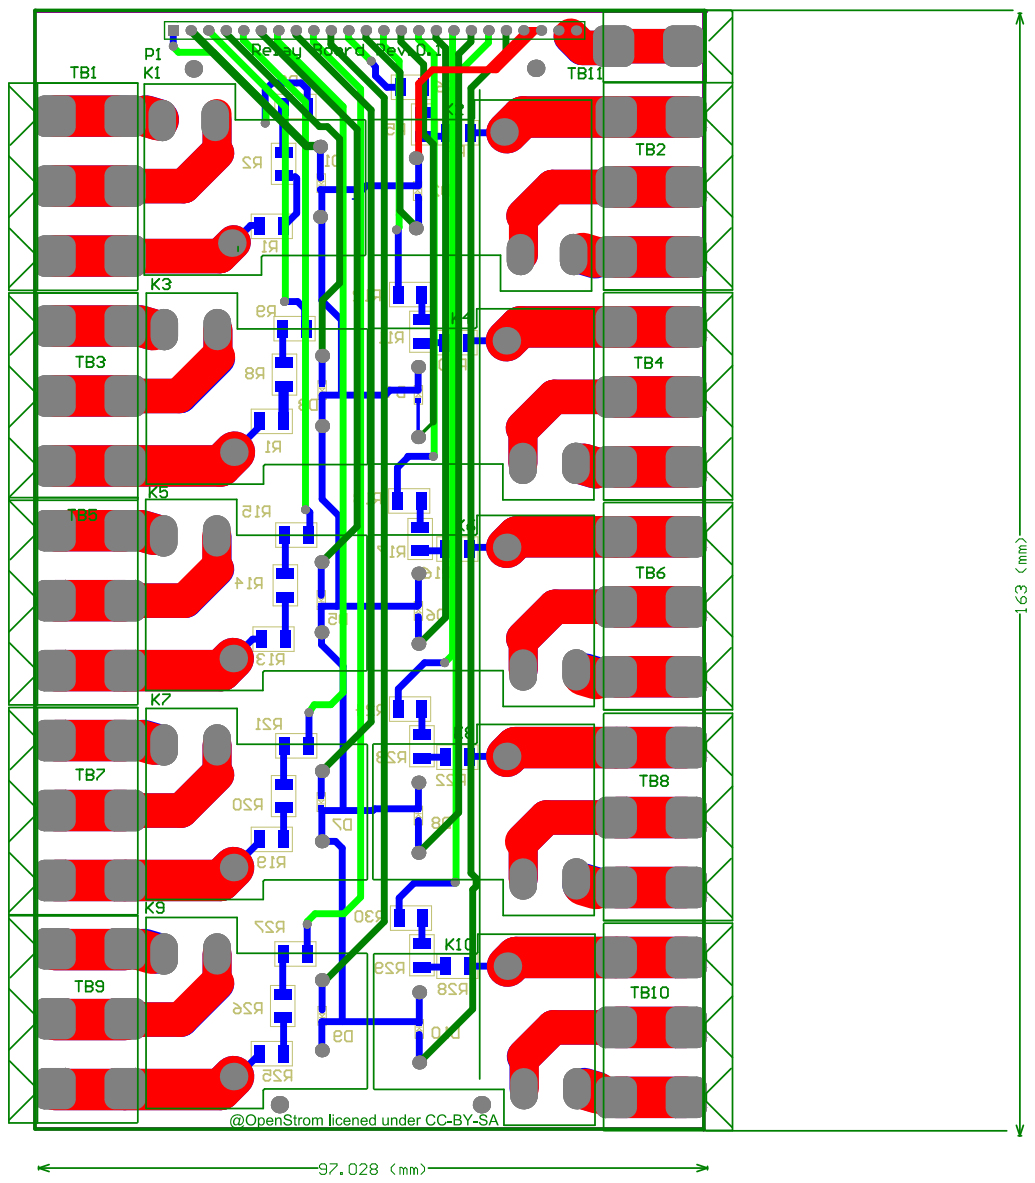
[picture p113: page 1]
