mzeitler/openstrom/schematic/source - draft/PDF - for reference only/CPU-board-multi.pdf

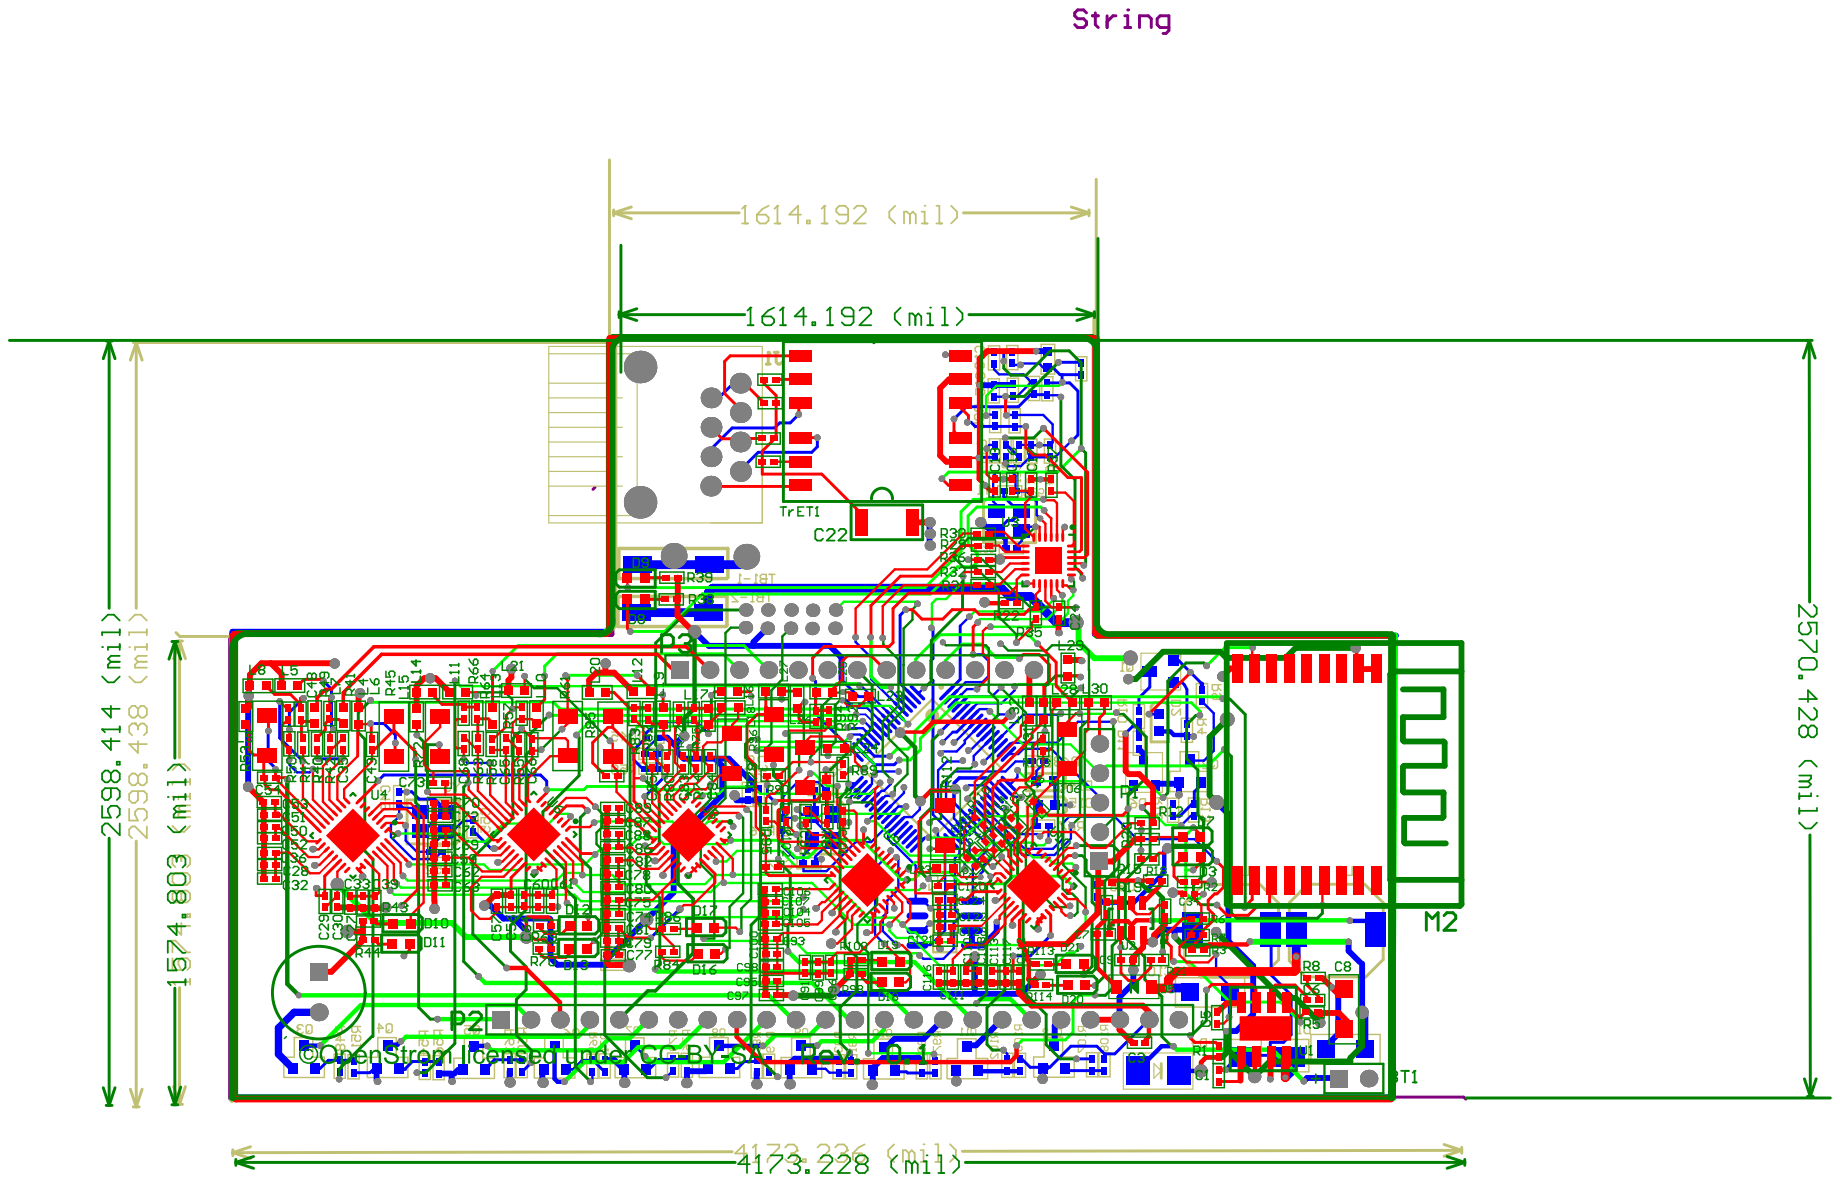
[picture p114: page 1]
