mzeitler/openstrom/schematic/source - draft/PDF - for reference only/Cross-section-sketch2.pdf

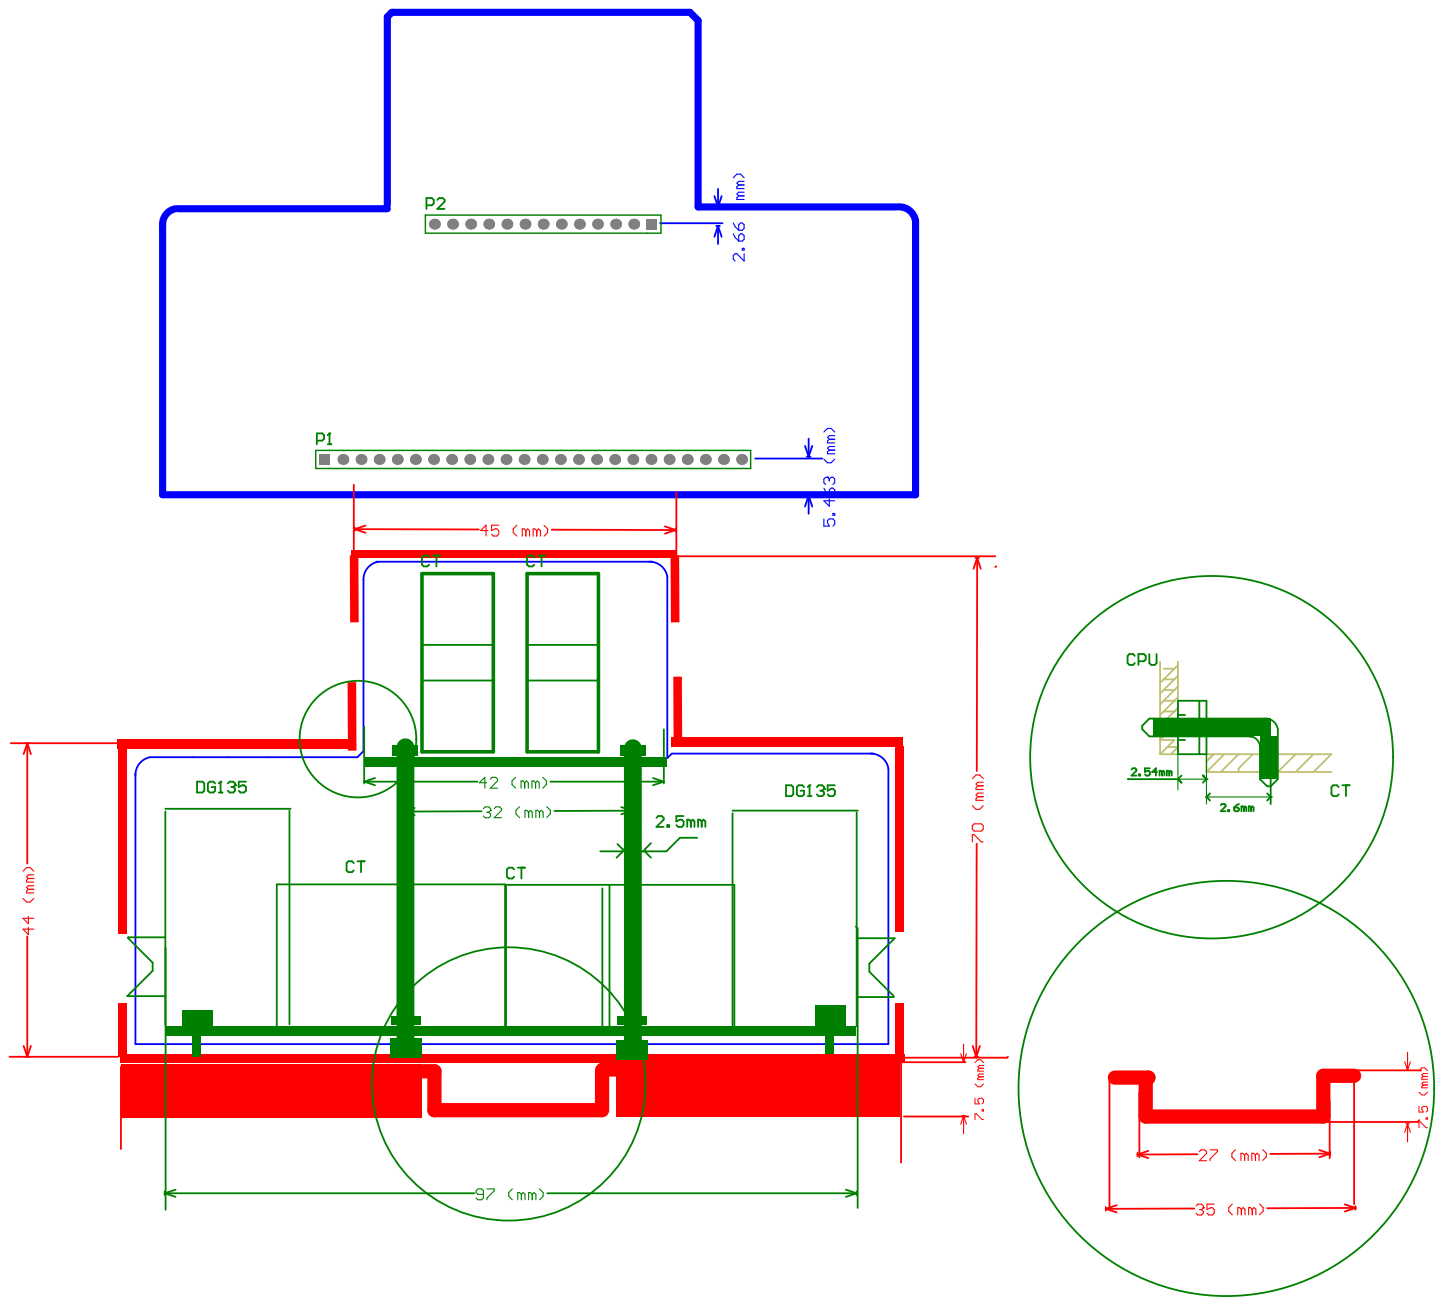
[picture p115: page 1]
