mzeitler/openstrom/schematic/source - draft/PDF - for reference only/Cross-sectionSM-sketch.pdf

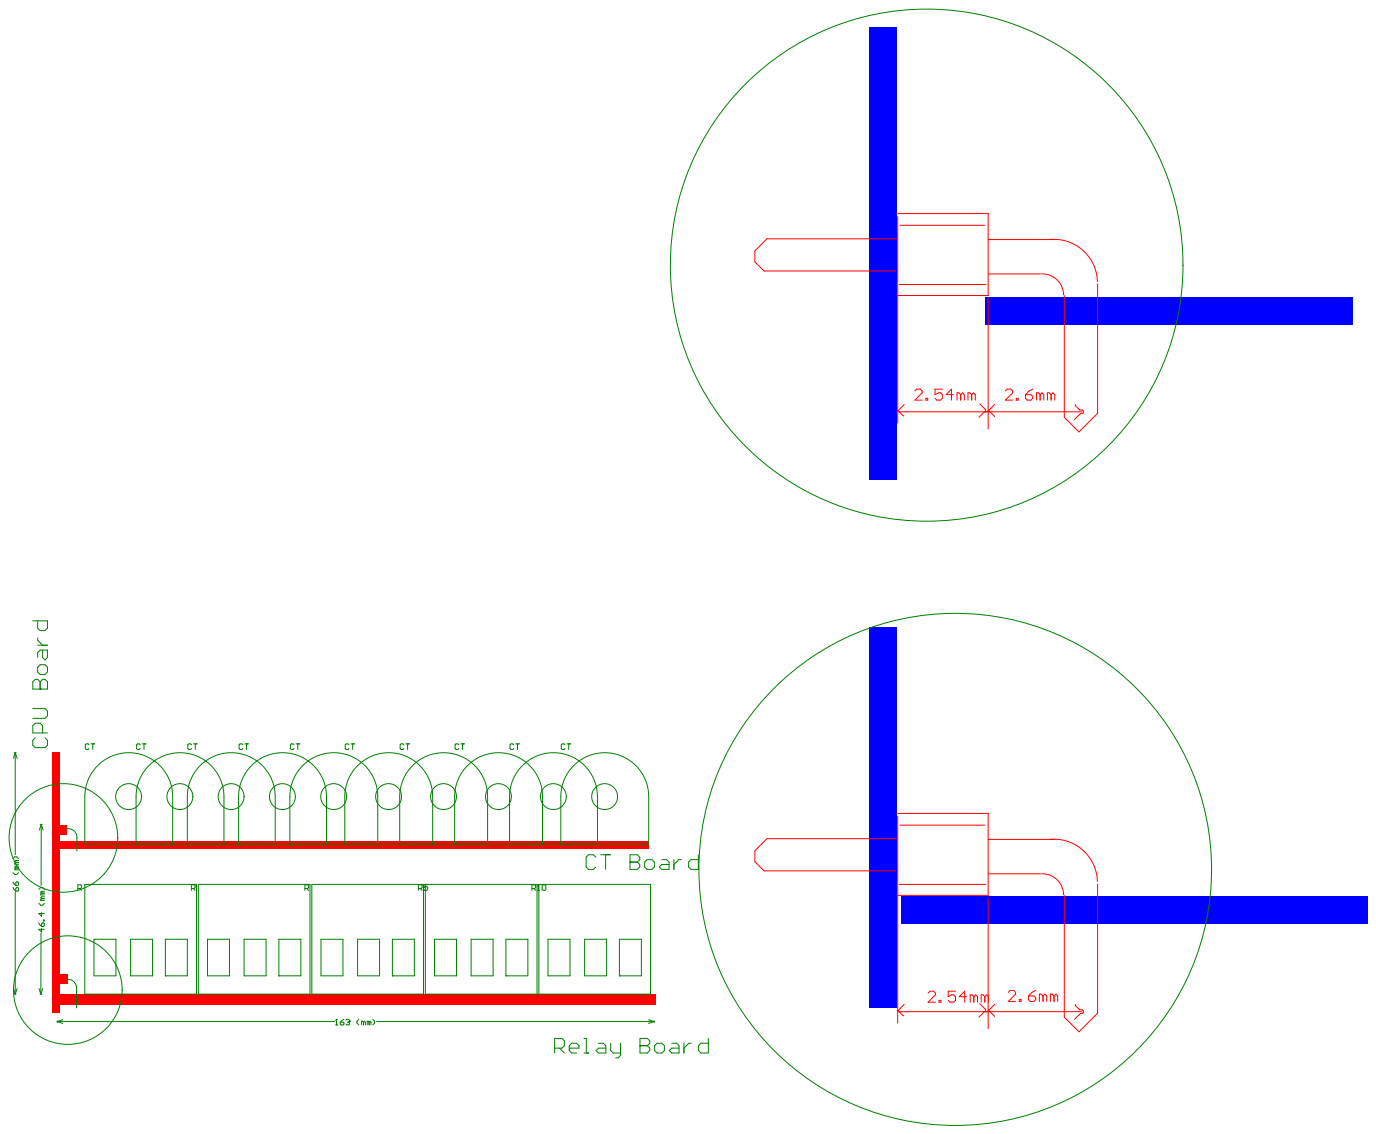
[picture p116: page 1]
