mzeitler/openstrom/schematic/source - draft/PDF - for reference only/CurrentTrans-board-multi.pdf

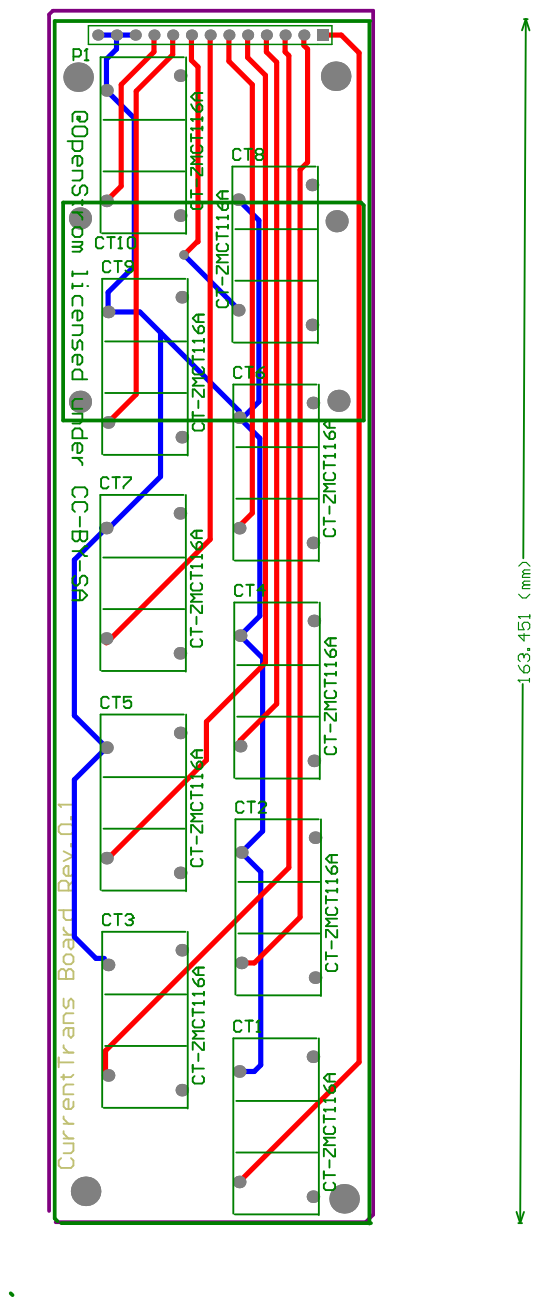
[picture p117: page 1]
