mzeitler/openstrom/firmware/communication stack/zigbee/src/system_config/default/system_config.h

/*******************************************************************************
  MPLAB Harmony System Configuration Header

  File Name:
    system_config.h

  Summary:
    Build-time configuration header for the system defined by this MPLAB Harmony
    project.

  Description:
    An MPLAB Project may have multiple configurations.  This file defines the
    build-time options for a single configuration.

  Remarks:
    This configuration header must not define any prototypes or data
    definitions (or include any files that do).  It only provides macro
    definitions for build-time configuration options that are not instantiated
    until used by another MPLAB Harmony module or application.

    Created with MPLAB Harmony Version 2.03
*******************************************************************************/

// DOM-IGNORE-BEGIN
/*******************************************************************************
Copyright (c) 2013-2015 released Microchip Technology Inc.  All rights reserved.

Microchip licenses to you the right to use, modify, copy and distribute
Software only when embedded on a Microchip microcontroller or digital signal
controller that is integrated into your product or third party product
(pursuant to the sublicense terms in the accompanying license agreement).

You should refer to the license agreement accompanying this Software for
additional information regarding your rights and obligations.

SOFTWARE AND DOCUMENTATION ARE PROVIDED AS IS WITHOUT WARRANTY OF ANY KIND,
EITHER EXPRESS OR IMPLIED, INCLUDING WITHOUT LIMITATION, ANY WARRANTY OF
MERCHANTABILITY, TITLE, NON-INFRINGEMENT AND FITNESS FOR A PARTICULAR PURPOSE.
IN NO EVENT SHALL MICROCHIP OR ITS LICENSORS BE LIABLE OR OBLIGATED UNDER
CONTRACT, NEGLIGENCE, STRICT LIABILITY, CONTRIBUTION, BREACH OF WARRANTY, OR
OTHER LEGAL EQUITABLE THEORY ANY DIRECT OR INDIRECT DAMAGES OR EXPENSES
INCLUDING BUT NOT LIMITED TO ANY INCIDENTAL, SPECIAL, INDIRECT, PUNITIVE OR
CONSEQUENTIAL DAMAGES, LOST PROFITS OR LOST DATA, COST OF PROCUREMENT OF
SUBSTITUTE GOODS, TECHNOLOGY, SERVICES, OR ANY CLAIMS BY THIRD PARTIES
(INCLUDING BUT NOT LIMITED TO ANY DEFENSE THEREOF), OR OTHER SIMILAR COSTS.
*******************************************************************************/
// DOM-IGNORE-END

#ifndef _SYSTEM_CONFIG_H
#define _SYSTEM_CONFIG_H

// *****************************************************************************
// *****************************************************************************
// Section: Included Files
// *****************************************************************************
// *****************************************************************************
/*  This section Includes other configuration headers necessary to completely
    define this configuration.
*/


// DOM-IGNORE-BEGIN
#ifdef __cplusplus  // Provide C++ Compatibility

extern "C" {

#endif
// DOM-IGNORE-END

// *****************************************************************************
// *****************************************************************************
// Section: System Service Configuration
// *****************************************************************************
// *****************************************************************************
// *****************************************************************************
/* Common System Service Configuration Options
*/
#define SYS_VERSION_STR           "2.03"
#define SYS_VERSION               20300

// *****************************************************************************
/* Clock System Service Configuration Options
*/
#define SYS_CLK_FREQ                        80000000ul
#define SYS_CLK_BUS_PERIPHERAL_1            80000000ul
#define SYS_CLK_UPLL_BEFORE_DIV2_FREQ       48000000ul
#define SYS_CLK_CONFIG_PRIMARY_XTAL         0ul
#define SYS_CLK_CONFIG_SECONDARY_XTAL       32768ul
   
/*** Ports System Service Configuration ***/
#define SYS_PORT_AD1PCFG        ~0xbfbf
#define SYS_PORT_CNPUE          0x0
#define SYS_PORT_CNEN           0x0
#define SYS_PORT_B_TRIS         0xFFBF
#define SYS_PORT_B_LAT          0x0000
#define SYS_PORT_B_ODC          0x0000

#define SYS_PORT_C_TRIS         0xFFFF
#define SYS_PORT_C_LAT          0x0000
#define SYS_PORT_C_ODC          0x0000

#define SYS_PORT_D_TRIS         0xFDFF
#define SYS_PORT_D_LAT          0x0000
#define SYS_PORT_D_ODC          0x0000

#define SYS_PORT_E_TRIS         0xFFFF
#define SYS_PORT_E_LAT          0x0000
#define SYS_PORT_E_ODC          0x0000

#define SYS_PORT_F_TRIS         0xFFFF
#define SYS_PORT_F_LAT          0x0000
#define SYS_PORT_F_ODC          0x0000

#define SYS_PORT_G_TRIS         0xFFFB
#define SYS_PORT_G_LAT          0x0000
#define SYS_PORT_G_ODC          0x0000


/*** Command Processor System Service Configuration ***/
#define SYS_CMD_ENABLE
#define SYS_CMD_DEVICE_MAX_INSTANCES    SYS_CONSOLE_DEVICE_MAX_INSTANCES
#define SYS_CMD_PRINT_BUFFER_SIZE       8192
#define SYS_CMD_BUFFER_DMA_READY
#define SYS_CMD_REMAP_SYS_CONSOLE_MESSAGE

/*** Console System Service Configuration ***/

#define SYS_CONSOLE_OVERRIDE_STDIO
#define SYS_CONSOLE_DEVICE_MAX_INSTANCES        2
#define SYS_CONSOLE_INSTANCES_NUMBER            1
#define SYS_CONSOLE_UART_IDX               DRV_USART_INDEX_0
#define SYS_CONSOLE_UART_BAUD_RATE_IDX     DRV_USART_BAUD_RATE_IDX0
#define SYS_CONSOLE_UART_RD_QUEUE_DEPTH    1
#define SYS_CONSOLE_UART_WR_QUEUE_DEPTH    64
#define SYS_CONSOLE_BUFFER_DMA_READY



/*** Interrupt System Service Configuration ***/
#define SYS_INT                     true

// *****************************************************************************
// *****************************************************************************
// Section: Driver Configuration
// *****************************************************************************
// *****************************************************************************

/*** SPI Driver Configuration ***/
#define DRV_SPI_NUMBER_OF_MODULES		3
/*** Driver Compilation and static configuration options. ***/
/*** Select SPI compilation units.***/
#define DRV_SPI_POLLED 				1
#define DRV_SPI_ISR 				0
#define DRV_SPI_MASTER 				1
#define DRV_SPI_SLAVE 				0
#define DRV_SPI_RM 					1
#define DRV_SPI_EBM 				0
#define DRV_SPI_8BIT 				1
#define DRV_SPI_16BIT 				0
#define DRV_SPI_32BIT 				0
#define DRV_SPI_DMA 				0

/*** SPI Driver Static Allocation Options ***/
#define DRV_SPI_INSTANCES_NUMBER 		1
#define DRV_SPI_CLIENTS_NUMBER 			1
#define DRV_SPI_ELEMENTS_PER_QUEUE 		10
// *****************************************************************************
/* USART Driver Configuration Options
*/
#define DRV_USART_INTERRUPT_MODE                    true

#define DRV_USART_BYTE_MODEL_SUPPORT                false

#define DRV_USART_READ_WRITE_MODEL_SUPPORT          true

#define DRV_USART_BUFFER_QUEUE_SUPPORT              true

#define DRV_USART_CLIENTS_NUMBER                    1
#define DRV_USART_INSTANCES_NUMBER                  1

#define DRV_USART_PERIPHERAL_ID_IDX0                USART_ID_1
#define DRV_USART_OPER_MODE_IDX0                    DRV_USART_OPERATION_MODE_NORMAL
#define DRV_USART_OPER_MODE_DATA_IDX0               
#define DRV_USART_INIT_FLAG_WAKE_ON_START_IDX0      false
#define DRV_USART_INIT_FLAG_AUTO_BAUD_IDX0          false
#define DRV_USART_INIT_FLAG_STOP_IN_IDLE_IDX0       false
#define DRV_USART_INIT_FLAGS_IDX0                   0
#define DRV_USART_BRG_CLOCK_IDX0                    80000000
#define DRV_USART_BAUD_RATE_IDX0                    9600
#define DRV_USART_LINE_CNTRL_IDX0                   DRV_USART_LINE_CONTROL_8NONE1
#define DRV_USART_HANDSHAKE_MODE_IDX0               DRV_USART_HANDSHAKE_NONE
#define DRV_USART_XMIT_INT_SRC_IDX0                 INT_SOURCE_USART_1_TRANSMIT
#define DRV_USART_RCV_INT_SRC_IDX0                  INT_SOURCE_USART_1_RECEIVE
#define DRV_USART_ERR_INT_SRC_IDX0                  INT_SOURCE_USART_1_ERROR
#define DRV_USART_INT_VECTOR_IDX0                   INT_VECTOR_UART1
#define DRV_USART_INT_PRIORITY_IDX0                 INT_PRIORITY_LEVEL1
#define DRV_USART_INT_SUB_PRIORITY_IDX0             INT_SUBPRIORITY_LEVEL0

#define DRV_USART_XMIT_QUEUE_SIZE_IDX0              10
#define DRV_USART_RCV_QUEUE_SIZE_IDX0               10


#define DRV_USART_POWER_STATE_IDX0                  SYS_MODULE_POWER_RUN_FULL

#define DRV_USART_QUEUE_DEPTH_COMBINED              20

// *****************************************************************************
// *****************************************************************************
// Section: Middleware & Other Library Configuration
// *****************************************************************************
// *****************************************************************************



// *****************************************************************************
// *****************************************************************************
// Section: Application Configuration
// *****************************************************************************
// *****************************************************************************
/*** Application Defined Pins ***/


/*** Application Instance 0 Configuration ***/

//DOM-IGNORE-BEGIN
#ifdef __cplusplus
}
#endif
//DOM-IGNORE-END

#endif // _SYSTEM_CONFIG_H
/*******************************************************************************
 End of File
*/
