mzeitler/openstrom/firmware/prototype - final/firmware/src/system_config/default/framework/peripheral/ports/processor/ports_p32mx795f512h.h

/* Created by plibgen $Revision: 1.31 $ */

#ifndef _PORTS_P32MX795F512H_H
#define _PORTS_P32MX795F512H_H

/* Section 1 - Enumerate instances, define constants, VREGs */

#include <xc.h>
#include <stdbool.h>

#include "peripheral/peripheral_common_32bit.h"

/* Default definition used for all API dispatch functions */
#ifndef PLIB_INLINE_API
    #define PLIB_INLINE_API extern inline
#endif

/* Default definition used for all other functions */
#ifndef PLIB_INLINE
    #define PLIB_INLINE extern inline
#endif

typedef enum {

    PORTS_ID_0 = 0,
    PORTS_NUMBER_OF_MODULES = 1

} PORTS_MODULE_ID;

typedef enum {

    PORTS_PIN_MODE_ANALOG = 0,
    PORTS_PIN_MODE_DIGITAL = 1

} PORTS_PIN_MODE;

typedef enum {

    CN8 = 8,
    CN9 = 9,
    CN10 = 10,
    CN11 = 11,
    CN7 = 7,
    CN6 = 6,
    CN5 = 5,
    CN4 = 4,
    CN3 = 3,
    CN2 = 2,
    CN12 = 12,
    CN17 = 17,
    CN18 = 18,
    CN1 = 1,
    CN0 = 0,
    CN13 = 13,
    CN14 = 14,
    CN15 = 15,
    CN16 = 16

} PORTS_CHANGE_NOTICE_PIN;

typedef enum {

    CHANGE_NOTICE_PIN_0 = 0x00001,
    CHANGE_NOTICE_PIN_1 = 0x00002,
    CHANGE_NOTICE_PIN_2 = 0x00004,
    CHANGE_NOTICE_PIN_3 = 0x00008,
    CHANGE_NOTICE_PIN_4 = 0x00010,
    CHANGE_NOTICE_PIN_5 = 0x00020,
    CHANGE_NOTICE_PIN_6 = 0x00040,
    CHANGE_NOTICE_PIN_7 = 0x00080,
    CHANGE_NOTICE_PIN_8 = 0x00100,
    CHANGE_NOTICE_PIN_9 = 0x00200,
    CHANGE_NOTICE_PIN_10 = 0x00400,
    CHANGE_NOTICE_PIN_11 = 0x00800,
    CHANGE_NOTICE_PIN_12 = 0x01000,
    CHANGE_NOTICE_PIN_13 = 0x02000,
    CHANGE_NOTICE_PIN_14 = 0x04000,
    CHANGE_NOTICE_PIN_15 = 0x08000,
    CHANGE_NOTICE_PIN_16 = 0x10000,
    CHANGE_NOTICE_PIN_17 = 0x20000,
    CHANGE_NOTICE_PIN_18 = 0x40000,
    CHANGE_NOTICE_PIN_ALL = 0x7FFFF

} PORTS_CN_PIN;

typedef enum {

    PORTS_ANALOG_PIN_0 = 0,
    PORTS_ANALOG_PIN_1 = 1,
    PORTS_ANALOG_PIN_2 = 2,
    PORTS_ANALOG_PIN_3 = 3,
    PORTS_ANALOG_PIN_4 = 4,
    PORTS_ANALOG_PIN_5 = 5,
    PORTS_ANALOG_PIN_6 = 6,
    PORTS_ANALOG_PIN_7 = 7,
    PORTS_ANALOG_PIN_8 = 8,
    PORTS_ANALOG_PIN_9 = 9,
    PORTS_ANALOG_PIN_10 = 10,
    PORTS_ANALOG_PIN_11 = 11,
    PORTS_ANALOG_PIN_12 = 12,
    PORTS_ANALOG_PIN_13 = 13,
    PORTS_ANALOG_PIN_14 = 14,
    PORTS_ANALOG_PIN_15 = 15

} PORTS_ANALOG_PIN;

typedef enum {

    PORTS_AN_PIN_0 = 0x0001,
    PORTS_AN_PIN_1 = 0x0002,
    PORTS_AN_PIN_2 = 0x0004,
    PORTS_AN_PIN_3 = 0x0008,
    PORTS_AN_PIN_4 = 0x0010,
    PORTS_AN_PIN_5 = 0x0020,
    PORTS_AN_PIN_6 = 0x0040,
    PORTS_AN_PIN_7 = 0x0080,
    PORTS_AN_PIN_8 = 0x0100,
    PORTS_AN_PIN_9 = 0x0200,
    PORTS_AN_PIN_10 = 0x0400,
    PORTS_AN_PIN_11 = 0x0800,
    PORTS_AN_PIN_12 = 0x1000,
    PORTS_AN_PIN_13 = 0x2000,
    PORTS_AN_PIN_14 = 0x4000,
    PORTS_AN_PIN_15 = 0x8000,
    PORTS_AN_PIN_ALL = 0xFFFF

} PORTS_AN_PIN;

typedef enum {

    PORTS_BIT_POS_0 = 0,
    PORTS_BIT_POS_1 = 1,
    PORTS_BIT_POS_2 = 2,
    PORTS_BIT_POS_3 = 3,
    PORTS_BIT_POS_4 = 4,
    PORTS_BIT_POS_5 = 5,
    PORTS_BIT_POS_6 = 6,
    PORTS_BIT_POS_7 = 7,
    PORTS_BIT_POS_8 = 8,
    PORTS_BIT_POS_9 = 9,
    PORTS_BIT_POS_10 = 10,
    PORTS_BIT_POS_11 = 11,
    PORTS_BIT_POS_12 = 12,
    PORTS_BIT_POS_13 = 13,
    PORTS_BIT_POS_14 = 14,
    PORTS_BIT_POS_15 = 15

} PORTS_BIT_POS;

typedef enum {

    PORTS_REMAP_INPUT_FUNCTION_NONE

} PORTS_REMAP_INPUT_FUNCTION;

typedef enum {

    PORTS_REMAP_INPUT_PIN_NONE

} PORTS_REMAP_INPUT_PIN;

typedef enum {

    PORTS_REMAP_OUTPUT_FUNCTION_NONE

} PORTS_REMAP_OUTPUT_FUNCTION;

typedef enum {

    PORTS_REMAP_OUTPUT_PIN_NONE

} PORTS_REMAP_OUTPUT_PIN;

typedef enum {

    PORT_CHANNEL_B = 0x01,
    PORT_CHANNEL_C = 0x02,
    PORT_CHANNEL_D = 0x03,
    PORT_CHANNEL_E = 0x04,
    PORT_CHANNEL_F = 0x05,
    PORT_CHANNEL_G = 0x06

} PORTS_CHANNEL;

typedef enum {

    PORTS_CHANGE_NOTICE_EDGE_NONE

} PORTS_CHANGE_NOTICE_EDGE;

typedef enum {

    PORTS_PIN_SLEW_RATE_NONE

} PORTS_PIN_SLEW_RATE;

typedef enum {

    PORTS_CHANGE_NOTICE_METHOD_NONE

} PORTS_CHANGE_NOTICE_METHOD;

/* Section 2 - Feature variant inclusion */

#define PLIB_TEMPLATE PLIB_INLINE
#include "../templates/ports_RemapInput_Unsupported.h"
#include "../templates/ports_RemapOutput_Unsupported.h"
#include "../templates/ports_PinMode_Non_PPS.h"
#include "../templates/ports_AnPinsMode_Non_PPS.h"
#include "../templates/ports_PortsRead_MCU32.h"
#include "../templates/ports_LatchRead_MCU32.h"
#include "../templates/ports_PortsWrite_MCU32.h"
#include "../templates/ports_PortsDirection_MCU32.h"
#include "../templates/ports_PortsOpenDrain_MCU32.h"
#include "../templates/ports_ChangeNotice_Default.h"
#include "../templates/ports_PinChangeNotice_Default.h"
#include "../templates/ports_ChangeNoticeInIdle_Default.h"
#include "../templates/ports_ChangeNoticePullup_Default.h"
#include "../templates/ports_PinModePerPort_Unsupported.h"
#include "../templates/ports_ChangeNoticePullDownPerPort_Unsupported.h"
#include "../templates/ports_ChangeNoticePullUpPerPort_Unsupported.h"
#include "../templates/ports_PinChangeNoticePerPort_Unsupported.h"
#include "../templates/ports_ChangeNoticePerPortTurnOn_Unsupported.h"
#include "../templates/ports_ChangeNoticeInIdlePerPort_Unsupported.h"
#include "../templates/ports_ChangeNoticePerPortStatus_Unsupported.h"
#include "../templates/ports_SlewRateControl_Unsupported.h"
#include "../templates/ports_ChannelChangeNoticeMethod_Unsupported.h"
#include "../templates/ports_ChangeNoticeEdgeControl_Unsupported.h"
#include "../templates/ports_ChangeNoticeEdgeStatus_Unsupported.h"

/* Section 3 - PLIB dispatch function definitions */

PLIB_INLINE_API void _PLIB_UNSUPPORTED PLIB_PORTS_RemapInput(PORTS_MODULE_ID index, PORTS_REMAP_INPUT_FUNCTION inputFunction, PORTS_REMAP_INPUT_PIN remapInputPin)
{
     PORTS_RemapInput_Unsupported(index, inputFunction, remapInputPin);
}

PLIB_INLINE_API bool PLIB_PORTS_ExistsRemapInput(PORTS_MODULE_ID index)
{
     return PORTS_ExistsRemapInput_Unsupported(index);
}

PLIB_INLINE_API void _PLIB_UNSUPPORTED PLIB_PORTS_RemapOutput(PORTS_MODULE_ID index, PORTS_REMAP_OUTPUT_FUNCTION outputFunction, PORTS_REMAP_OUTPUT_PIN remapOutputPin)
{
     PORTS_RemapOutput_Unsupported(index, outputFunction, remapOutputPin);
}

PLIB_INLINE_API bool PLIB_PORTS_ExistsRemapOutput(PORTS_MODULE_ID index)
{
     return PORTS_ExistsRemapOutput_Unsupported(index);
}

PLIB_INLINE_API void PLIB_PORTS_PinModeSelect(PORTS_MODULE_ID index, PORTS_ANALOG_PIN pin, PORTS_PIN_MODE mode)
{
     PORTS_PinModeSelect_Non_PPS(index, pin, mode);
}

PLIB_INLINE_API bool PLIB_PORTS_ExistsPinMode(PORTS_MODULE_ID index)
{
     return PORTS_ExistsPinMode_Non_PPS(index);
}

PLIB_INLINE_API void PLIB_PORTS_AnPinsModeSelect(PORTS_MODULE_ID index, PORTS_AN_PIN anPins, PORTS_PIN_MODE mode)
{
     PORTS_AnPinsModeSelect_Non_PPS(index, anPins, mode);
}

PLIB_INLINE_API bool PLIB_PORTS_ExistsAnPinsMode(PORTS_MODULE_ID index)
{
     return PORTS_ExistsAnPinsMode_Non_PPS(index);
}

PLIB_INLINE_API bool PLIB_PORTS_PinGet(PORTS_MODULE_ID index, PORTS_CHANNEL channel, PORTS_BIT_POS bitPos)
{
     return PORTS_PinGet_MCU32(index, channel, bitPos);
}

PLIB_INLINE_API PORTS_DATA_TYPE PLIB_PORTS_Read(PORTS_MODULE_ID index, PORTS_CHANNEL channel)
{
     return PORTS_Read_MCU32(index, channel);
}

PLIB_INLINE_API bool PLIB_PORTS_ExistsPortsRead(PORTS_MODULE_ID index)
{
     return PORTS_ExistsPortsRead_MCU32(index);
}

PLIB_INLINE_API bool PLIB_PORTS_PinGetLatched(PORTS_MODULE_ID index, PORTS_CHANNEL channel, PORTS_BIT_POS bitPos)
{
     return PORTS_PinGetLatched_MCU32(index, channel, bitPos);
}

PLIB_INLINE_API PORTS_DATA_TYPE PLIB_PORTS_ReadLatched(PORTS_MODULE_ID index, PORTS_CHANNEL channel)
{
     return PORTS_ReadLatched_MCU32(index, channel);
}

PLIB_INLINE_API bool PLIB_PORTS_ExistsLatchRead(PORTS_MODULE_ID index)
{
     return PORTS_ExistsLatchRead_MCU32(index);
}

PLIB_INLINE_API void PLIB_PORTS_PinWrite(PORTS_MODULE_ID index, PORTS_CHANNEL channel, PORTS_BIT_POS bitPos, bool value)
{
     PORTS_PinWrite_MCU32(index, channel, bitPos, value);
}

PLIB_INLINE_API void PLIB_PORTS_PinSet(PORTS_MODULE_ID index, PORTS_CHANNEL channel, PORTS_BIT_POS bitPos)
{
     PORTS_PinSet_MCU32(index, channel, bitPos);
}

PLIB_INLINE_API void PLIB_PORTS_PinClear(PORTS_MODULE_ID index, PORTS_CHANNEL channel, PORTS_BIT_POS bitPos)
{
     PORTS_PinClear_MCU32(index, channel, bitPos);
}

PLIB_INLINE_API void PLIB_PORTS_PinToggle(PORTS_MODULE_ID index, PORTS_CHANNEL channel, PORTS_BIT_POS bitPos)
{
     PORTS_PinToggle_MCU32(index, channel, bitPos);
}

PLIB_INLINE_API void PLIB_PORTS_Write(PORTS_MODULE_ID index, PORTS_CHANNEL channel, PORTS_DATA_TYPE value)
{
     PORTS_Write_MCU32(index, channel, value);
}

PLIB_INLINE_API void PLIB_PORTS_Set(PORTS_MODULE_ID index, PORTS_CHANNEL channel, PORTS_DATA_TYPE value, PORTS_DATA_MASK mask)
{
     PORTS_Set_MCU32(index, channel, value, mask);
}

PLIB_INLINE_API void PLIB_PORTS_Toggle(PORTS_MODULE_ID index, PORTS_CHANNEL channel, PORTS_DATA_MASK toggleMask)
{
     PORTS_Toggle_MCU32(index, channel, toggleMask);
}

PLIB_INLINE_API void PLIB_PORTS_Clear(PORTS_MODULE_ID index, PORTS_CHANNEL channel, PORTS_DATA_MASK clearMask)
{
     PORTS_Clear_MCU32(index, channel, clearMask);
}

PLIB_INLINE_API bool PLIB_PORTS_ExistsPortsWrite(PORTS_MODULE_ID index)
{
     return PORTS_ExistsPortsWrite_MCU32(index);
}

PLIB_INLINE_API void PLIB_PORTS_PinDirectionInputSet(PORTS_MODULE_ID index, PORTS_CHANNEL channel, PORTS_BIT_POS bitPos)
{
     PORTS_PinDirectionInputSet_MCU32(index, channel, bitPos);
}

PLIB_INLINE_API void PLIB_PORTS_PinDirectionOutputSet(PORTS_MODULE_ID index, PORTS_CHANNEL channel, PORTS_BIT_POS bitPos)
{
     PORTS_PinDirectionOutputSet_MCU32(index, channel, bitPos);
}

PLIB_INLINE_API void PLIB_PORTS_DirectionInputSet(PORTS_MODULE_ID index, PORTS_CHANNEL channel, PORTS_DATA_MASK mask)
{
     PORTS_DirectionInputSet_MCU32(index, channel, mask);
}

PLIB_INLINE_API void PLIB_PORTS_DirectionOutputSet(PORTS_MODULE_ID index, PORTS_CHANNEL channel, PORTS_DATA_MASK mask)
{
     PORTS_DirectionOutputSet_MCU32(index, channel, mask);
}

PLIB_INLINE_API PORTS_DATA_MASK PLIB_PORTS_DirectionGet(PORTS_MODULE_ID index, PORTS_CHANNEL channel)
{
     return PORTS_DirectionGet_MCU32(index, channel);
}

PLIB_INLINE_API bool PLIB_PORTS_ExistsPortsDirection(PORTS_MODULE_ID index)
{
     return PORTS_ExistsPortsDirection_MCU32(index);
}

PLIB_INLINE_API void PLIB_PORTS_PinOpenDrainEnable(PORTS_MODULE_ID index, PORTS_CHANNEL channel, PORTS_BIT_POS bitPos)
{
     PORTS_PinOpenDrainEnable_MCU32(index, channel, bitPos);
}

PLIB_INLINE_API void PLIB_PORTS_PinOpenDrainDisable(PORTS_MODULE_ID index, PORTS_CHANNEL channel, PORTS_BIT_POS bitPos)
{
     PORTS_PinOpenDrainDisable_MCU32(index, channel, bitPos);
}

PLIB_INLINE_API void PLIB_PORTS_OpenDrainEnable(PORTS_MODULE_ID index, PORTS_CHANNEL channel, PORTS_DATA_MASK mask)
{
     PORTS_OpenDrainEnable_MCU32(index, channel, mask);
}

PLIB_INLINE_API void PLIB_PORTS_OpenDrainDisable(PORTS_MODULE_ID index, PORTS_CHANNEL channel, PORTS_DATA_MASK mask)
{
     PORTS_OpenDrainDisable_MCU32(index, channel, mask);
}

PLIB_INLINE_API bool PLIB_PORTS_ExistsPortsOpenDrain(PORTS_MODULE_ID index)
{
     return PORTS_ExistsPortsOpenDrain_MCU32(index);
}

PLIB_INLINE_API void PLIB_PORTS_ChangeNoticeEnable(PORTS_MODULE_ID index)
{
     PORTS_ChangeNoticeEnable_Default(index);
}

PLIB_INLINE_API void PLIB_PORTS_ChangeNoticeDisable(PORTS_MODULE_ID index)
{
     PORTS_ChangeNoticeDisable_Default(index);
}

PLIB_INLINE_API bool PLIB_PORTS_ExistsChangeNotice(PORTS_MODULE_ID index)
{
     return PORTS_ExistsChangeNotice_Default(index);
}

PLIB_INLINE_API void PLIB_PORTS_PinChangeNoticeEnable(PORTS_MODULE_ID index, PORTS_CHANGE_NOTICE_PIN pinNum)
{
     PORTS_PinChangeNoticeEnable_Default(index, pinNum);
}

PLIB_INLINE_API void PLIB_PORTS_PinChangeNoticeDisable(PORTS_MODULE_ID index, PORTS_CHANGE_NOTICE_PIN pinNum)
{
     PORTS_PinChangeNoticeDisable_Default(index, pinNum);
}

PLIB_INLINE_API void PLIB_PORTS_CnPinsEnable(PORTS_MODULE_ID index, PORTS_CN_PIN cnPins)
{
     PORTS_CnPinsEnable_Default(index, cnPins);
}

PLIB_INLINE_API void PLIB_PORTS_CnPinsDisable(PORTS_MODULE_ID index, PORTS_CN_PIN cnPins)
{
     PORTS_CnPinsDisable_Default(index, cnPins);
}

PLIB_INLINE_API bool PLIB_PORTS_ExistsPinChangeNotice(PORTS_MODULE_ID index)
{
     return PORTS_ExistsPinChangeNotice_Default(index);
}

PLIB_INLINE_API void PLIB_PORTS_ChangeNoticeInIdleEnable(PORTS_MODULE_ID index)
{
     PORTS_ChangeNoticeInIdleEnable_Default(index);
}

PLIB_INLINE_API void PLIB_PORTS_ChangeNoticeInIdleDisable(PORTS_MODULE_ID index)
{
     PORTS_ChangeNoticeInIdleDisable_Default(index);
}

PLIB_INLINE_API bool PLIB_PORTS_ExistsChangeNoticeInIdle(PORTS_MODULE_ID index)
{
     return PORTS_ExistsChangeNoticeInIdle_Default(index);
}

PLIB_INLINE_API void PLIB_PORTS_ChangeNoticePullUpEnable(PORTS_MODULE_ID index, PORTS_CHANGE_NOTICE_PIN pinNum)
{
     PORTS_ChangeNoticePullUpEnable_Default(index, pinNum);
}

PLIB_INLINE_API void PLIB_PORTS_ChangeNoticePullUpDisable(PORTS_MODULE_ID index, PORTS_CHANGE_NOTICE_PIN pinNum)
{
     PORTS_ChangeNoticePullUpDisable_Default(index, pinNum);
}

PLIB_INLINE_API void PLIB_PORTS_CnPinsPullUpEnable(PORTS_MODULE_ID index, PORTS_CN_PIN cnPins)
{
     PORTS_CnPinsPullUpEnable_Default(index, cnPins);
}

PLIB_INLINE_API void PLIB_PORTS_CnPinsPullUpDisable(PORTS_MODULE_ID index, PORTS_CN_PIN cnPins)
{
     PORTS_CnPinsPullUpDisable_Default(index, cnPins);
}

PLIB_INLINE_API bool PLIB_PORTS_ExistsChangeNoticePullUp(PORTS_MODULE_ID index)
{
     return PORTS_ExistsChangeNoticePullUp_Default(index);
}

PLIB_INLINE_API void _PLIB_UNSUPPORTED PLIB_PORTS_PinModePerPortSelect(PORTS_MODULE_ID index, PORTS_CHANNEL channel, PORTS_BIT_POS bitPos, PORTS_PIN_MODE mode)
{
     PORTS_PinModePerPortSelect_Unsupported(index, channel, bitPos, mode);
}

PLIB_INLINE_API void _PLIB_UNSUPPORTED PLIB_PORTS_ChannelModeSelect(PORTS_MODULE_ID index, PORTS_CHANNEL channel, PORTS_DATA_MASK modeMask, PORTS_PIN_MODE mode)
{
     PORTS_ChannelModeSelect_Unsupported(index, channel, modeMask, mode);
}

PLIB_INLINE_API bool PLIB_PORTS_ExistsPinModePerPort(PORTS_MODULE_ID index)
{
     return PORTS_ExistsPinModePerPort_Unsupported(index);
}

PLIB_INLINE_API void _PLIB_UNSUPPORTED PLIB_PORTS_ChangeNoticePullDownPerPortEnable(PORTS_MODULE_ID index, PORTS_CHANNEL channel, PORTS_BIT_POS bitPos)
{
     PORTS_ChangeNoticePullDownPerPortEnable_Unsupported(index, channel, bitPos);
}

PLIB_INLINE_API void _PLIB_UNSUPPORTED PLIB_PORTS_ChangeNoticePullDownPerPortDisable(PORTS_MODULE_ID index, PORTS_CHANNEL channel, PORTS_BIT_POS bitPos)
{
     PORTS_ChangeNoticePullDownPerPortDisable_Unsupported(index, channel, bitPos);
}

PLIB_INLINE_API void _PLIB_UNSUPPORTED PLIB_PORTS_ChannelChangeNoticePullDownEnable(PORTS_MODULE_ID index, PORTS_CHANNEL channel, PORTS_DATA_MASK mask)
{
     PORTS_ChannelChangeNoticePullDownEnable_Unsupported(index, channel, mask);
}

PLIB_INLINE_API void _PLIB_UNSUPPORTED PLIB_PORTS_ChannelChangeNoticePullDownDisable(PORTS_MODULE_ID index, PORTS_CHANNEL channel, PORTS_DATA_MASK mask)
{
     PORTS_ChannelChangeNoticePullDownDisable_Unsupported(index, channel, mask);
}

PLIB_INLINE_API bool PLIB_PORTS_ExistsChangeNoticePullDownPerPort(PORTS_MODULE_ID index)
{
     return PORTS_ExistsChangeNoticePullDownPerPort_Unsupported(index);
}

PLIB_INLINE_API void _PLIB_UNSUPPORTED PLIB_PORTS_ChangeNoticePullUpPerPortEnable(PORTS_MODULE_ID index, PORTS_CHANNEL channel, PORTS_BIT_POS bitPos)
{
     PORTS_ChangeNoticePullUpPerPortEnable_Unsupported(index, channel, bitPos);
}

PLIB_INLINE_API void _PLIB_UNSUPPORTED PLIB_PORTS_ChangeNoticePullUpPerPortDisable(PORTS_MODULE_ID index, PORTS_CHANNEL channel, PORTS_BIT_POS bitPos)
{
     PORTS_ChangeNoticePullUpPerPortDisable_Unsupported(index, channel, bitPos);
}

PLIB_INLINE_API void _PLIB_UNSUPPORTED PLIB_PORTS_ChannelChangeNoticePullUpEnable(PORTS_MODULE_ID index, PORTS_CHANNEL channel, PORTS_DATA_MASK mask)
{
     PORTS_ChannelChangeNoticePullUpEnable_Unsupported(index, channel, mask);
}

PLIB_INLINE_API void _PLIB_UNSUPPORTED PLIB_PORTS_ChannelChangeNoticePullUpDisable(PORTS_MODULE_ID index, PORTS_CHANNEL channel, PORTS_DATA_MASK mask)
{
     PORTS_ChannelChangeNoticePullUpDisable_Unsupported(index, channel, mask);
}

PLIB_INLINE_API bool PLIB_PORTS_ExistsChangeNoticePullUpPerPort(PORTS_MODULE_ID index)
{
     return PORTS_ExistsChangeNoticePullUpPerPort_Unsupported(index);
}

PLIB_INLINE_API void _PLIB_UNSUPPORTED PLIB_PORTS_PinChangeNoticePerPortEnable(PORTS_MODULE_ID index, PORTS_CHANNEL channel, PORTS_BIT_POS bitPos)
{
     PORTS_PinChangeNoticePerPortEnable_Unsupported(index, channel, bitPos);
}

PLIB_INLINE_API void _PLIB_UNSUPPORTED PLIB_PORTS_PinChangeNoticePerPortDisable(PORTS_MODULE_ID index, PORTS_CHANNEL channel, PORTS_BIT_POS bitPos)
{
     PORTS_PinChangeNoticePerPortDisable_Unsupported(index, channel, bitPos);
}

PLIB_INLINE_API void _PLIB_UNSUPPORTED PLIB_PORTS_ChannelChangeNoticeEnable(PORTS_MODULE_ID index, PORTS_CHANNEL channel, PORTS_DATA_MASK mask)
{
     PORTS_ChannelChangeNoticeEnable_Unsupported(index, channel, mask);
}

PLIB_INLINE_API void _PLIB_UNSUPPORTED PLIB_PORTS_ChannelChangeNoticeDisable(PORTS_MODULE_ID index, PORTS_CHANNEL channel, PORTS_DATA_MASK mask)
{
     PORTS_ChannelChangeNoticeDisable_Unsupported(index, channel, mask);
}

PLIB_INLINE_API bool PLIB_PORTS_ExistsPinChangeNoticePerPort(PORTS_MODULE_ID index)
{
     return PORTS_ExistsPinChangeNoticePerPort_Unsupported(index);
}

PLIB_INLINE_API void _PLIB_UNSUPPORTED PLIB_PORTS_ChangeNoticePerPortTurnOn(PORTS_MODULE_ID index, PORTS_CHANNEL channel)
{
     PORTS_ChangeNoticePerPortTurnOn_Unsupported(index, channel);
}

PLIB_INLINE_API void _PLIB_UNSUPPORTED PLIB_PORTS_ChangeNoticePerPortTurnOff(PORTS_MODULE_ID index, PORTS_CHANNEL channel)
{
     PORTS_ChangeNoticePerPortTurnOff_Unsupported(index, channel);
}

PLIB_INLINE_API bool PLIB_PORTS_ExistsChangeNoticePerPortTurnOn(PORTS_MODULE_ID index)
{
     return PORTS_ExistsChangeNoticePerPortTurnOn_Unsupported(index);
}

PLIB_INLINE_API void _PLIB_UNSUPPORTED PLIB_PORTS_ChangeNoticeInIdlePerPortEnable(PORTS_MODULE_ID index, PORTS_CHANNEL channel)
{
     PORTS_ChangeNoticeInIdlePerPortEnable_Unsupported(index, channel);
}

PLIB_INLINE_API void _PLIB_UNSUPPORTED PLIB_PORTS_ChangeNoticeInIdlePerPortDisable(PORTS_MODULE_ID index, PORTS_CHANNEL channel)
{
     PORTS_ChangeNoticeInIdlePerPortDisable_Unsupported(index, channel);
}

PLIB_INLINE_API bool PLIB_PORTS_ExistsChangeNoticePerPortInIdle(PORTS_MODULE_ID index)
{
     return PORTS_ExistsChangeNoticePerPortInIdle_Unsupported(index);
}

PLIB_INLINE_API bool _PLIB_UNSUPPORTED PLIB_PORTS_ChangeNoticePerPortHasOccurred(PORTS_MODULE_ID index, PORTS_CHANNEL channel, PORTS_BIT_POS bitPos)
{
     return PORTS_ChangeNoticePerPortHasOccurred_Unsupported(index, channel, bitPos);
}

PLIB_INLINE_API bool PLIB_PORTS_ExistsChangeNoticePerPortStatus(PORTS_MODULE_ID index)
{
     return PORTS_ExistsChangeNoticePerPortStatus_Unsupported(index);
}

PLIB_INLINE_API void _PLIB_UNSUPPORTED PLIB_PORTS_ChannelSlewRateSelect(PORTS_MODULE_ID index, PORTS_CHANNEL channel, PORTS_DATA_MASK channelMask, PORTS_PIN_SLEW_RATE slewRate)
{
     PORTS_ChannelSlewRateSelect_Unsupported(index, channel, channelMask, slewRate);
}

PLIB_INLINE_API PORTS_PIN_SLEW_RATE _PLIB_UNSUPPORTED PLIB_PORTS_PinSlewRateGet(PORTS_MODULE_ID index, PORTS_CHANNEL channel, PORTS_BIT_POS bitPos)
{
     return PORTS_PinSlewRateGet_Unsupported(index, channel, bitPos);
}

PLIB_INLINE_API bool PLIB_PORTS_ExistsSlewRateControl(PORTS_MODULE_ID index)
{
     return PORTS_ExistsSlewRateControl_Unsupported(index);
}

PLIB_INLINE_API void _PLIB_UNSUPPORTED PLIB_PORTS_ChannelChangeNoticeMethodSelect(PORTS_MODULE_ID index, PORTS_CHANNEL channel, PORTS_CHANGE_NOTICE_METHOD changeNoticeMethod)
{
     PORTS_ChannelChangeNoticeMethodSelect_Unsupported(index, channel, changeNoticeMethod);
}

PLIB_INLINE_API PORTS_CHANGE_NOTICE_METHOD _PLIB_UNSUPPORTED PLIB_PORTS_ChannelChangeNoticeMethodGet(PORTS_MODULE_ID index, PORTS_CHANNEL channel)
{
     return PORTS_ChannelChangeNoticeMethodGet_Unsupported(index, channel);
}

PLIB_INLINE_API bool PLIB_PORTS_ExistsChannelChangeNoticeMethod(PORTS_MODULE_ID index)
{
     return PORTS_ExistsChannelChangeNoticeMethod_Unsupported(index);
}

PLIB_INLINE_API void _PLIB_UNSUPPORTED PLIB_PORTS_ChannelChangeNoticeEdgeEnable(PORTS_MODULE_ID index, PORTS_CHANNEL channel, PORTS_DATA_MASK edgeRisingMask, PORTS_DATA_MASK edgeFallingMask)
{
     PORTS_ChannelChangeNoticeEdgeEnable_Unsupported(index, channel, edgeRisingMask, edgeFallingMask);
}

PLIB_INLINE_API void _PLIB_UNSUPPORTED PLIB_PORTS_ChannelChangeNoticeEdgeDisable(PORTS_MODULE_ID index, PORTS_CHANNEL channel, PORTS_DATA_MASK edgeRisingMask, PORTS_DATA_MASK edgeFallingMask)
{
     PORTS_ChannelChangeNoticeEdgeDisable_Unsupported(index, channel, edgeRisingMask, edgeFallingMask);
}

PLIB_INLINE_API bool _PLIB_UNSUPPORTED PLIB_PORTS_PinChangeNoticeEdgeIsEnabled(PORTS_MODULE_ID index, PORTS_CHANNEL channel, PORTS_BIT_POS bitPos, PORTS_CHANGE_NOTICE_EDGE cnEdgeType)
{
     return PORTS_PinChangeNoticeEdgeIsEnabled_Unsupported(index, channel, bitPos, cnEdgeType);
}

PLIB_INLINE_API bool PLIB_PORTS_ExistsChangeNoticeEdgeControl(PORTS_MODULE_ID index)
{
     return PORTS_ExistsChangeNoticeEdgeControl_Unsupported(index);
}

PLIB_INLINE_API bool _PLIB_UNSUPPORTED PLIB_PORTS_PinChangeNoticeEdgeHasOccurred(PORTS_MODULE_ID index, PORTS_CHANNEL channel, PORTS_BIT_POS bitPos)
{
     return PORTS_PinChangeNoticeEdgeHasOccurred_Unsupported(index, channel, bitPos);
}

PLIB_INLINE_API bool PLIB_PORTS_ExistsChangeNoticeEdgeStatus(PORTS_MODULE_ID index)
{
     return PORTS_ExistsChangeNoticeEdgeStatus_Unsupported(index);
}

#endif
