mzeitler/openstrom/firmware/prototype - final/firmware/src/system_config/default/framework/peripheral/can/processor/can_p32xxxx.h

#ifndef _PLIB_CAN_P32XXXX_H
#define _PLIB_CAN_P32XXXX_H


#if defined(__PIC32CZ2038CA70144__)
    #include "can_p32cz2038ca70144.h"

#elif defined(__32MK1024GPE100__)
    #include "can_p32mk1024gpe100.h"

#elif defined(__32MK1024GPD100__)
    #include "can_p32mk1024gpd100.h"

#elif defined(__32MK1024GPE064__)
    #include "can_p32mk1024gpe064.h"

#elif defined(__32MK1024GPD064__)
    #include "can_p32mk1024gpd064.h"

#elif defined(__32MK0512GPE100__)
    #include "can_p32mk0512gpe100.h"
	
#elif defined(__32MK0512GPD100__)
    #include "can_p32mk0512gpd100.h"

#elif defined(__32MK0512GPE064__)
    #include "can_p32mk0512gpe064.h"

#elif defined(__32MK0512GPD064__)
    #include "can_p32mk0512gpd064.h"

#elif defined(__32MK1024MCF100__)
    #include "can_p32mk1024mcf100.h"

#elif defined(__32MK1024MCF064__)
    #include "can_p32mk1024mcf064.h"

#elif defined(__32MK0512MCF100__)
    #include "can_p32mk0512mcf100.h"

#elif defined(__32MK0512MCF064__)
    #include "can_p32mk0512mcf064.h"
	
#elif defined(__32MX120F064H__)
    #include "can_p32mx120f064h.h"

#elif defined(__32MX130F128H__)
    #include "can_p32mx130f128h.h"

#elif defined(__32MX130F128L__)
    #include "can_p32mx130f128l.h"

#elif defined(__32MX230F128H__)
    #include "can_p32mx230f128h.h"

#elif defined(__32MX230F128L__)
    #include "can_p32mx230f128l.h"
	
#elif defined(__32MX530F128H__)
    #include "can_p32mx530f128h.h"

#elif defined(__32MX530F128L__)
    #include "can_p32mx530f128l.h"

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

#elif defined(__32MZ2064DAA169__)
    #include "can_p32mz2064daa169.h"

#elif defined(__32MZ2064DAA176__)
    #include "can_p32mz2064daa176.h"

#elif defined(__32MZ2064DAA288__)
    #include "can_p32mz2064daa288.h"

#elif defined(__32MZ2064DAB169__)
    #include "can_p32mz2064dab169.h"

#elif defined(__32MZ2064DAB176__)
    #include "can_p32mz2064dab176.h"

#elif defined(__32MZ2064DAB288__)
    #include "can_p32mz2064dab288.h"

#elif defined(__32MZ2064DAG169__)
    #include "can_p32mz2064dag169.h"

#elif defined(__32MZ2064DAG176__)
    #include "can_p32mz2064dag176.h"

#elif defined(__32MZ2064DAH169__)
    #include "can_p32mz2064dah169.h"

#elif defined(__32MZ2064DAH176__)
    #include "can_p32mz2064dah176.h"
	
#elif defined(__32WK2057GPB132__)
    #include "can_p32wk2057gpb132.h"
	
#elif defined(__32WK2057GPD132__)
    #include "can_p32wk2057gpd132.h"	
	
#elif defined(__32MXGENERIC__)
    #include "can_p32mxgeneric.h"

#elif defined(__32M4KCORE__)
    #include "can_p32m4kcore.h"

#else
    #error Unknown processor!
#endif

#endif//_PLIB_CAN_P32XXXX_H
