mzeitler/openstrom/firmware/prototype - final/firmware/src/system_config/default/framework/system/ports/src/sys_ports_static.c

/*******************************************************************************
  SYS PORTS Static Functions for PORTS System Service

  Company:
    Microchip Technology Inc.

  File Name:
    sys_ports_static.c

  Summary:
    SYS PORTS static function implementations for the Ports System Service.

  Description:
    The Ports System Service provides a simple interface to manage the ports
    on Microchip microcontrollers. This file defines the static implementation for the 
    Ports System Service.
    
  Remarks:
    Static functions incorporate all system ports configuration settings as
    determined by the user via the Microchip Harmony Configurator GUI.  It provides 
    static version of the routines, eliminating the need for an object ID or 
    object handle.

*******************************************************************************/

//DOM-IGNORE-BEGIN
/*******************************************************************************
Copyright (c) 2013 released Microchip Technology Inc.  All rights reserved.

Microchip licenses to you the right to use, modify, copy and distribute
Software only when embedded on a Microchip microcontroller or digital signal
controller that is integrated into your product or third party product
(pursuant to the sublicense terms in the accompanying license agreement).

You should refer to the license agreement accompanying this Software for
additional information regarding your rights and obligations.

SOFTWARE AND DOCUMENTATION ARE PROVIDED AS IS WITHOUT WARRANTY OF ANY KIND,
EITHER EXPRESS OR IMPLIED, INCLUDING WITHOUT LIMITATION, ANY WARRANTY OF
MERCHANTABILITY, TITLE, NON-INFRINGEMENT AND FITNESS FOR A PARTICULAR PURPOSE.
IN NO EVENT SHALL MICROCHIP OR ITS LICENSORS BE LIABLE OR OBLIGATED UNDER
CONTRACT, NEGLIGENCE, STRICT LIABILITY, CONTRIBUTION, BREACH OF WARRANTY, OR
OTHER LEGAL EQUITABLE THEORY ANY DIRECT OR INDIRECT DAMAGES OR EXPENSES
INCLUDING BUT NOT LIMITED TO ANY INCIDENTAL, SPECIAL, INDIRECT, PUNITIVE OR
CONSEQUENTIAL DAMAGES, LOST PROFITS OR LOST DATA, COST OF PROCUREMENT OF
SUBSTITUTE GOODS, TECHNOLOGY, SERVICES, OR ANY CLAIMS BY THIRD PARTIES
(INCLUDING BUT NOT LIMITED TO ANY DEFENSE THEREOF), OR OTHER SIMILAR COSTS.
*******************************************************************************/
//DOM-IGNORE-END

#include "system_config.h"
#include "system/ports/sys_ports.h"
#include "peripheral/devcon/plib_devcon.h"
#include "peripheral/ports/plib_ports.h"
#include "peripheral/int/plib_int.h"

/******************************************************************************
  Function:
    SYS_PORTS_Initialize(void)

  Summary:
    Initializes Ports System Service

  Description:
    This function initializes different port pins/channels to the desired state.
    It also remaps the pins to the desired specific function.

  Remarks:
    None.
*/
void SYS_PORTS_Initialize(void)
{

    /* AN and CN Pins Initialization */
    PLIB_PORTS_AnPinsModeSelect(PORTS_ID_0, SYS_PORT_AD1PCFG, PORTS_PIN_MODE_DIGITAL);
    PLIB_PORTS_CnPinsPullUpEnable(PORTS_ID_0, SYS_PORT_CNPUE);
    PLIB_PORTS_CnPinsEnable(PORTS_ID_0, SYS_PORT_CNEN);
    PLIB_PORTS_ChangeNoticeEnable(PORTS_ID_0);

    PLIB_PORTS_Read(PORTS_ID_0, PORT_CHANNEL_B);    
    PLIB_PORTS_Read(PORTS_ID_0, PORT_CHANNEL_C);    
    PLIB_PORTS_Read(PORTS_ID_0, PORT_CHANNEL_D);    
    PLIB_PORTS_Read(PORTS_ID_0, PORT_CHANNEL_E);    
    PLIB_PORTS_Read(PORTS_ID_0, PORT_CHANNEL_F);    
    PLIB_PORTS_Read(PORTS_ID_0, PORT_CHANNEL_G);    
    PLIB_INT_SourceFlagClear(INT_ID_0, INT_SOURCE_CHANGE_NOTICE);         
    PLIB_INT_SourceEnable(INT_ID_0, INT_SOURCE_CHANGE_NOTICE);
    PLIB_INT_VectorPrioritySet(INT_ID_0, INT_VECTOR_CN, INT_PRIORITY_LEVEL1);
    PLIB_INT_VectorSubPrioritySet(INT_ID_0, INT_VECTOR_CN, INT_SUBPRIORITY_LEVEL0);          
    
    
    /* PORT B Initialization */
    PLIB_PORTS_OpenDrainEnable(PORTS_ID_0, PORT_CHANNEL_B, SYS_PORT_B_ODC);
    PLIB_PORTS_Write( PORTS_ID_0, PORT_CHANNEL_B,  SYS_PORT_B_LAT);
	PLIB_PORTS_DirectionOutputSet( PORTS_ID_0, PORT_CHANNEL_B,  SYS_PORT_B_TRIS ^ 0xFFFF);
    
    /* PORT C Initialization */
    PLIB_PORTS_OpenDrainEnable(PORTS_ID_0, PORT_CHANNEL_C, SYS_PORT_C_ODC);
    PLIB_PORTS_Write( PORTS_ID_0, PORT_CHANNEL_C,  SYS_PORT_C_LAT);
	PLIB_PORTS_DirectionOutputSet( PORTS_ID_0, PORT_CHANNEL_C,  SYS_PORT_C_TRIS ^ 0xFFFF);
    
    /* PORT D Initialization */
    PLIB_PORTS_OpenDrainEnable(PORTS_ID_0, PORT_CHANNEL_D, SYS_PORT_D_ODC);
    PLIB_PORTS_Write( PORTS_ID_0, PORT_CHANNEL_D,  SYS_PORT_D_LAT);
	PLIB_PORTS_DirectionOutputSet( PORTS_ID_0, PORT_CHANNEL_D,  SYS_PORT_D_TRIS ^ 0xFFFF);
    
    /* PORT E Initialization */
    PLIB_PORTS_OpenDrainEnable(PORTS_ID_0, PORT_CHANNEL_E, SYS_PORT_E_ODC);
    PLIB_PORTS_Write( PORTS_ID_0, PORT_CHANNEL_E,  SYS_PORT_E_LAT);
	PLIB_PORTS_DirectionOutputSet( PORTS_ID_0, PORT_CHANNEL_E,  SYS_PORT_E_TRIS ^ 0xFFFF);
    
    /* PORT F Initialization */
    PLIB_PORTS_OpenDrainEnable(PORTS_ID_0, PORT_CHANNEL_F, SYS_PORT_F_ODC);
    PLIB_PORTS_Write( PORTS_ID_0, PORT_CHANNEL_F,  SYS_PORT_F_LAT);
	PLIB_PORTS_DirectionOutputSet( PORTS_ID_0, PORT_CHANNEL_F,  SYS_PORT_F_TRIS ^ 0xFFFF);
    
    /* PORT G Initialization */
    PLIB_PORTS_OpenDrainEnable(PORTS_ID_0, PORT_CHANNEL_G, SYS_PORT_G_ODC);
    PLIB_PORTS_Write( PORTS_ID_0, PORT_CHANNEL_G,  SYS_PORT_G_LAT);
	PLIB_PORTS_DirectionOutputSet( PORTS_ID_0, PORT_CHANNEL_G,  SYS_PORT_G_TRIS ^ 0xFFFF);
    
}

/******************************************************************************
  Function:
    PORTS_DATA_TYPE SYS_PORTS_Read( PORTS_MODULE_ID index, PORTS_CHANNEL channel )

  Summary:
    Reads the data from the I/O port.

  Description:
    This function reads the data from the I/O port.

  Remarks:
    None.
*/

PORTS_DATA_TYPE SYS_PORTS_Read( PORTS_MODULE_ID index, PORTS_CHANNEL channel )
{
    return PLIB_PORTS_Read( index, channel );
}


/******************************************************************************
  Function:
    void SYS_PORTS_Write( PORTS_MODULE_ID index, PORTS_CHANNEL channel,
                      		PORTS_DATA_TYPE value )

  Summary:
    Writes the data from the I/O port.

  Description:
    This function writes the data to the I/O port.

  Remarks:
    None.
*/

void SYS_PORTS_Write( PORTS_MODULE_ID index,
                      PORTS_CHANNEL channel,
                      PORTS_DATA_TYPE value )
{
    PLIB_PORTS_Write( index, channel, value );
}

/******************************************************************************
  Function:
    PORTS_DATA_TYPE SYS_PORTS_LatchedGet( PORTS_MODULE_ID index, PORTS_CHANNEL channel )

  Summary:
    Reads the data driven on the I/O port.

  Description:
    This function reads the data driven on the I/O port.

  Remarks:
    None.
*/

PORTS_DATA_TYPE SYS_PORTS_LatchedGet( PORTS_MODULE_ID index, PORTS_CHANNEL channel )
{
    SYS_ASSERT(false, "This API is not supported on this device");
    /* TODO: Call corresponding PLIB API */
    return 0;
}

/******************************************************************************
  Function:
    void SYS_PORTS_Set( PORTS_MODULE_ID index, PORTS_CHANNEL channel,
	                         PORTS_DATA_TYPE value,
                         PORTS_DATA_MASK mask )

  Summary:
    Sets the selected digital port/latch based on the mask.

  Description:
    This function sets the selected digital port/latch relative to the mask.

  Remarks:
    None.
*/

void SYS_PORTS_Set( PORTS_MODULE_ID index, PORTS_CHANNEL channel,
                    PORTS_DATA_TYPE value,
                    PORTS_DATA_MASK mask )
{
    PLIB_PORTS_Set( index, channel, value, mask );
}


/******************************************************************************
  Function:
    void SYS_PORTS_Clear ( PORTS_MODULE_ID index, PORTS_CHANNEL channel,
                           PORTS_DATA_MASK clearMask )

  Summary:
    Clears the selected digital port.

  Description:
    This function clears the selected digital port.

  Remarks:
    None.
*/

void SYS_PORTS_Clear ( PORTS_MODULE_ID index, PORTS_CHANNEL channel,
                           PORTS_DATA_MASK clearMask )
{
    PLIB_PORTS_Clear ( index, channel, clearMask );
}


/******************************************************************************
  Function:
    void SYS_PORTS_DirectionSelect( PORTS_MODULE_ID index,
								SYS_PORTS_PIN_DIRECTION pinDir,
								PORTS_CHANNEL channel,
								PORTS_DATA_MASK mask )
  Summary:
    Enables the direction for the selected port.

  Description:
    This function enables the direction for the selected port.

  Remarks:
    None.
*/

void SYS_PORTS_DirectionSelect( PORTS_MODULE_ID index,
                             SYS_PORTS_PIN_DIRECTION pinDir,
                             PORTS_CHANNEL channel,
                             PORTS_DATA_MASK mask )
{
    if (pinDir == SYS_PORTS_DIRECTION_INPUT)
    {
        PLIB_PORTS_DirectionInputSet(index, channel, mask);
    }
    else
    {
        PLIB_PORTS_DirectionOutputSet(index, channel, mask);
    }
}


/******************************************************************************
  Function:
    PORTS_DATA_MASK SYS_PORTS_DirectionGet( PORTS_MODULE_ID index,
                                            PORTS_CHANNEL channel )

  Summary:
    Reads the port direction for the selected port.

  Description:
    This function reads the port direction for the selected port.

  Remarks:
    None.
*/

PORTS_DATA_MASK SYS_PORTS_DirectionGet( PORTS_MODULE_ID index, PORTS_CHANNEL channel )
{
    return PLIB_PORTS_DirectionGet( index, channel );
}


/******************************************************************************
  Function:
    void SYS_PORTS_Toggle( PORTS_MODULE_ID index, PORTS_CHANNEL channel,
                           PORTS_DATA_MASK toggleMask )

  Summary:
    Toggles the selected digital port pins.

  Description:
    This function toggles the selected digital port pins.

  Remarks:
    None.
*/

void SYS_PORTS_Toggle( PORTS_MODULE_ID index, PORTS_CHANNEL channel,
                       PORTS_DATA_MASK toggleMask )
{
    PLIB_PORTS_Toggle( index, channel, toggleMask );
}


/******************************************************************************
  Function:
    void SYS_PORTS_OpenDrainEnable( PORTS_MODULE_ID index, PORTS_CHANNEL channel,
                                     PORTS_DATA_MASK mask )

  Summary:
    Enables the open drain functionality for the selected port.

  Description:
    This function enables the open drain functionality for the selected port.

  Remarks:
    None.
*/

void SYS_PORTS_OpenDrainEnable( PORTS_MODULE_ID index, PORTS_CHANNEL channel,
                                PORTS_DATA_MASK mask )
{
#if defined(PLIB_PORTS_ExistsPortsOpenDrain)
    if(PLIB_PORTS_ExistsPortsOpenDrain(index))
    {
        PLIB_PORTS_OpenDrainEnable( index, channel, mask );
    }
#endif
}


/******************************************************************************
  Function:
    void SYS_PORTS_OpenDrainDisable( PORTS_MODULE_ID index, PORTS_CHANNEL channel,
                                     PORTS_DATA_MASK mask )

  Summary:
    Disables the open drain functionality for the selected port.

  Description:
    This function disables the open drain functionality for the selected port.

  Remarks:
    None.
*/

void SYS_PORTS_OpenDrainDisable( PORTS_MODULE_ID index, PORTS_CHANNEL channel,
                                 PORTS_DATA_MASK mask )
{
#if defined(PLIB_PORTS_ExistsPortsOpenDrain)
    if(PLIB_PORTS_ExistsPortsOpenDrain(index))
    {
        PLIB_PORTS_OpenDrainDisable( index, channel, mask );
    }
#endif
}

// *****************************************************************************
/* Function:
    PORTS_DATA_TYPE SYS_PORTS_InterruptStatusGet
    ( 
        PORTS_MODULE_ID index, 
        PORTS_CHANNEL channel 
    )

  Summary:
    Reads the data from the I/O port.
	<p><b>Implementation:</b> Dynamic</p>

  Description:
    This function reads the data from the I/O port.

*/

PORTS_DATA_TYPE SYS_PORTS_InterruptStatusGet
( 
    PORTS_MODULE_ID index, 
    PORTS_CHANNEL channel 
)
{
    SYS_ASSERT(false, "This API is not supported on this device");
    return 0;
}

// *****************************************************************************
// *****************************************************************************
// Section: SYS Change Notification Pins Routines
// *****************************************************************************
// *****************************************************************************

/******************************************************************************
  Function:
    void SYS_PORTS_ChangeNotificationGlobalEnable( PORTS_MODULE_ID index )

  Summary:
    Globally enables the change notification.

  Description:
    This function globally enables the change notification.

  Remarks:
    None.
*/

void SYS_PORTS_ChangeNotificationGlobalEnable( PORTS_MODULE_ID index )
{
#if defined(PLIB_PORTS_ExistsChangeNotice)
    if(PLIB_PORTS_ExistsChangeNotice(index))
    {
        PLIB_PORTS_ChangeNoticeEnable( index );
    }
#endif
}

/******************************************************************************
  Function:
    void SYS_PORTS_ChangeNotificationGlobalDisable( PORTS_MODULE_ID index )

  Summary:
    Globally disables the change notification.

  Description:
    This function globally disables the change notification.

  Remarks:
    None.
*/

void SYS_PORTS_ChangeNotificationGlobalDisable( PORTS_MODULE_ID index )
{
#if defined(PLIB_PORTS_ExistsChangeNotice)
    if(PLIB_PORTS_ExistsChangeNotice(index))
    {
        PLIB_PORTS_ChangeNoticeDisable( index );
    }
#endif
}

/******************************************************************************
  Function:
    void SYS_PORTS_GlobalChangeNotificationDisable( PORTS_MODULE_ID index )

  Summary:
    Globally disables the change notification for the selected port.

  Description:
    This function globally disables the change notification for the selected port.

  Remarks:
    None.
*/

void SYS_PORTS_GlobalChangeNotificationDisable( PORTS_MODULE_ID index )
{
#if defined(PLIB_PORTS_ExistsChangeNotice)
    if(PLIB_PORTS_ExistsChangeNotice(index))
    {
        PLIB_PORTS_ChangeNoticeDisable( index );
    }
#endif
}


/******************************************************************************
  Function:
    void SYS_PORTS_ChangeNotificationEnable( PORTS_MODULE_ID index,
                                             PORTS_CHANGE_NOTICE_PIN pinNum,
                                             SYS_PORTS_PULLUP_PULLDOWN_STATUS value )

  Summary:
    Enables the change notification for the selected port.

  Description:
    This function enables the change notification for the selected port.

  Remarks:
    None.
*/

void SYS_PORTS_ChangeNotificationEnable( PORTS_MODULE_ID index,
                                         PORTS_CHANGE_NOTICE_PIN pinNum,
                                         SYS_PORTS_PULLUP_PULLDOWN_STATUS value )
{
#if defined(PLIB_PORTS_ExistsChangeNoticePullUp)
    if(PLIB_PORTS_ExistsChangeNoticePullUp(index))
    {
        switch(value)
        {
            case SYS_PORTS_PULLUP_DISABLE:
                PLIB_PORTS_ChangeNoticePullUpDisable(index, pinNum);
                break;
            case SYS_PORTS_PULLUP_ENABLE:
                PLIB_PORTS_ChangeNoticePullUpEnable(index, pinNum);
                break;
        }
    }
#endif

#if defined(PLIB_PORTS_ExistsPinChangeNotice)
    if(PLIB_PORTS_ExistsPinChangeNotice(index))
    {
        PLIB_PORTS_PinChangeNoticeEnable( index, pinNum );
    }
#endif
}


/******************************************************************************
  Function:
    void SYS_PORTS_ChangeNotificationDisable( PORTS_MODULE_ID index,
                                              PORTS_CHANGE_NOTICE_PIN pinNum )

  Summary:
    Disables the change notification for the selected port.

  Description:
    This function disables the change notification for the selected port.

  Remarks:
    None.
*/

void SYS_PORTS_ChangeNotificationDisable( PORTS_MODULE_ID index,
                                          PORTS_CHANGE_NOTICE_PIN pinNum )
{
#if defined(PLIB_PORTS_ExistsPinChangeNotice)
    if(PLIB_PORTS_ExistsPinChangeNotice(index))
    {
        PLIB_PORTS_PinChangeNoticeDisable( index, pinNum );
    }
#endif
}


/******************************************************************************
  Function:
    void SYS_PORTS_ChangeNotificationInIdleModeEnable( PORTS_MODULE_ID index )

  Summary:
    Enables the change notification for the selected port in Sleep or Idle mode.

  Description:
    This function enables the change notification for the selected port in Sleep
    or Idle mode.

  Remarks:
    None.
*/

void SYS_PORTS_ChangeNotificationInIdleModeEnable( PORTS_MODULE_ID index )
{
#if defined(PLIB_PORTS_ExistsChangeNoticeInIdle)
    if(PLIB_PORTS_ExistsChangeNoticeInIdle(index))
    {
        PLIB_PORTS_ChangeNoticeInIdleEnable( index );
    }
#endif
}


// *****************************************************************************
/* Function:
    void SYS_PORTS_ChangeNotificationInIdleModeDisable( PORTS_MODULE_ID index)

  Summary:
    Disables the change notification for the selected port in Sleep or Idle mode.

  Description:
    This function disables the change notification for the selected port in Sleep
    or Idle mode.

  Remarks:
    None.
*/

void SYS_PORTS_ChangeNotificationInIdleModeDisable( PORTS_MODULE_ID index )
{
#if defined(PLIB_PORTS_ExistsChangeNoticeInIdle)
    if(PLIB_PORTS_ExistsChangeNoticeInIdle(index))
    {
        PLIB_PORTS_ChangeNoticeInIdleDisable( index );
    }
#endif
}


// *****************************************************************************
/* Function:
    void SYS_PORTS_ChangeNotificationPullUpEnable ( PORTS_MODULE_ID         index,
                                                    PORTS_CHANGE_NOTICE_PIN pinNum )

  Summary:
    Enables weak pull-up on change notification pin.

  Description:
    This function enables weak pull-up on change notification pin.

  Remarks:
    None.
*/

void SYS_PORTS_ChangeNotificationPullUpEnable ( PORTS_MODULE_ID         index,
                                                PORTS_CHANGE_NOTICE_PIN pinNum )
{
#if defined(PLIB_PORTS_ExistsChangeNoticePullUp)
    if(PLIB_PORTS_ExistsChangeNoticePullUp(index))
    {
        PLIB_PORTS_ChangeNoticePullUpEnable ( index, pinNum );
    }
#endif
}


// *****************************************************************************
/* Function:
    void SYS_PORTS_ChangeNotificationPullUpDisable ( PORTS_MODULE_ID         index,
                                                    PORTS_CHANGE_NOTICE_PIN pinNum )

  Summary:
    Disables pull-up on input change.

  Description:
    This function disables pull-up on input change.

  Remarks:
    None.
*/

void SYS_PORTS_ChangeNotificationPullUpDisable ( PORTS_MODULE_ID         index,
                                                PORTS_CHANGE_NOTICE_PIN pinNum )
{
#if defined(PLIB_PORTS_ExistsChangeNoticePullUp)
    if(PLIB_PORTS_ExistsChangeNoticePullUp(index))
    {
        PLIB_PORTS_ChangeNoticePullUpDisable ( index, pinNum );
    }
#endif
}


// *****************************************************************************
// *****************************************************************************
// Section: SYS PORT PINS Control Routines
// *****************************************************************************
// *****************************************************************************

// *****************************************************************************
/* Function:
    void SYS_PORTS_PinModeSelect ( PORTS_MODULE_ID index, PORTS_ANALOG_PIN pin,
    								PORTS_PIN_MODE mode)

  Summary:
    Enables the selected pin as analog or digital.

  Description:
    This function enables the selected pin as analog or digital.

 Remarks:
    None.
*/

void SYS_PORTS_PinModeSelect ( PORTS_MODULE_ID index, PORTS_ANALOG_PIN pin,
								PORTS_PIN_MODE mode)
{
#if defined(PLIB_PORTS_ExistsPinMode)
    if(PLIB_PORTS_ExistsPinMode(index))
    {
        PLIB_PORTS_PinModeSelect ( index, pin, mode);
    }
#endif
}
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
